kenneth558/plant_resistance_primary_perception_IN_DEVELOPMENT/the Biblical perspective.md

The principles relevant to the GWAAM-Sea Aid are found in several Bible verses, including the following:

Notice the name of the element within us that is being exercised when we practice this type of gardening:

 - If ye have faith, and doubt not, ye shall not only do this which is done to the fig tree, but also if ye shall 
   say unto this mountain, Be thou removed, and be thou cast into the sea; it shall be done. And all things,
   whatsoever ye shall ask in prayer, believing, ye shall receive. Matt 21:21-22

Notice the value God puts on that element:

 - But without faith it is impossible to please him    Heb. 11:6

Notice the pre-eminent importance of love (called "charity" in the KJV Bible; gr. "agape")

 - And now abideth faith, hope, charity, these three; but the greatest of these is charity. I Cor 13:13

Notice the acquisition order that will be acceptable for the beginner during their growth and maturation:

 - And beside this, giving all diligence, add to your faith virtue; and to virtue knowledge; And to knowledge
   temperance; and to temperance patience; and to patience godliness; And to godliness brotherly kindness; and to 
   brotherly kindness charity (love).   2 Peter 1:5

And finally, since Jesus made the connection between faith and prayer in that Matt. 21:22 verse above, notice the type of prayer and faith that will get things done:

 - The effectual fervent (the word "energetic" encapsulates both terms; gr. "energeo") prayer of a righteous man availeth much.

From all this, we see that developing the faith to affect plants is merely step 1 of a journey of which the destiny is love.  Stated another way, it will be very unbecoming, even ugly, for a person to exercise faith, yet not be intent on loving other people.

We also see from that verse that when we exert energy in support of our faith's actions that faith produces greater results.  Cleve Backster noticed the same thing in his experiments with plants.

Note that even though God values virtue, knowledge, and so on out to love more than faith, He'll be gracious to accept us to start with faith.

The elephant in the living room:  These teachings from heaven were kept hidden by God from the public until Jesus walked this earth and brought them to us.  Jesus says no one can come to the Father but through Jesus.  Although we've discovered that plants will respond to anyones' sentiments, thanks to the grace of God, God's real God-ordained starting point for our development along this path is Jesus:

 - "But as many as received him, to them gave he power to become the sons of God, even to them that believe on 
    his name"   John 1:12
    
What plants are recognizing in us is that mankind comes from a royal lineage.  God has placed us here intending that we choose that royalty once again, and in so doing, Jesus offers us a more abundant life:  "I am come that they might have life, and that they might have it more abundantly"   John 10:10  (the astute reader will notice additionally that Jesus has actually also come to give us life itself...there is something deep there for those who have an ear to hear...)

Jesus' statement in Matt. 21:21 is a prophecy that has yet to be fulfilled to the scale He stated it.  To the extent that we are now able to fulfill this good prophecy of His and we refuse to do so, we deprive Him of what He is worthy of.  I want to see that He is no longer deprived of the fulfillment of His words that He is worthy of.  With a little help from the real-time, instantaneous feedback that devices like the GWAAM-Sea Aid provide, people can learn the faith technique needed to bring fulfillment to that good prophecy of His.

## Wrap-up:</p>
Jesus cursed the fig tree, it withered away, and He said we would do the same [Matt 21:19-21](https://www.biblegateway.com/passage/?search=Matt+21%3A19-21&version=KJV):

#### 19 And when he saw a fig tree in the way, he came to it, and found nothing thereon, but leaves only, and said unto it, Let no fruit grow on thee henceforward for ever. And presently the fig tree withered away.
#### 20 And when the disciples saw it, they marvelled, saying, How soon is the fig tree withered away!
#### 21 Jesus answered and said unto them, Verily I say unto you, If ye have faith, and doubt not, ye shall not only do this which is done to the fig tree, but also if ye shall say unto this mountain, Be thou removed, and be thou cast into the sea; it shall be done.
#      
When we read this passage, we too often overlook the phrase "...ye shall not only do this which is done to the fig tree...".  But that oft-overlooked phrase contains just as profound a truth as the phrase following it about casting mountains!  Jesus did not condemn us if we should curse a plant, yet we must not forget [John 14:12](https://www.biblegateway.com/passage/?search=John+14%3A12&version=KJV):
#### Verily, verily, I say unto you, He that believeth on me, the works that I do shall he do also; and greater works than these shall he do; because I go unto my Father.
Ask yourself what a greater work might be than cursing a plant to kill it.  How about blessing a plant to cause its health to be better than normal?  [Mark 16:15](https://www.biblegateway.com/passage/?search=Mark+16%3A15&version=KJV):
#### And he said unto them, Go ye into all the world, and preach the gospel to every creature.
I draw your attention on the word "creature".  That includes plants!  And note that the definition of "gospel" is "good news"

In summary, Jesus accepted the fact that people would kill plants like fig trees with a curse but also said we will do greater than that.  It is with the hope that we will do far, *far* more of the latter than the former that I make the plans for this project freely available to everyone.  I am convinced that it is NOW time to demonstrate the truthfulness of the Bible in this context!  That is by monitoring the electrical resistance of plant tissue in vivo as it responds to sentiments of good news delivered to it from human beings that plants recognize as royalty in the creation.  To understate my point - it would be of great benefit for us to recognize that we are royalty, just as the plants recognize that humans are royalty in the creation.

[Galatians 4:1-7](https://www.biblegateway.com/passage/?search=Galatians+4%3A1-7&version=KJV):
#### 1 Now I say, That the heir, as long as he is a child, differeth nothing from a servant, though he be lord of all;
#### 2 But is under tutors and governors until the time appointed of the father.
#### 3 Even so we, when we were children, were in bondage under the elements of the world:
#### 4 But when the fulness of the time was come, God sent forth his Son, made of a woman, made under the law,
#### 5 To redeem them that were under the law, that we might receive the adoption of sons.
#### 6 And because ye are sons, God hath sent forth the Spirit of his Son into your hearts, crying, Abba, Father.
#### 7 Wherefore thou art no more a servant, but a son; and if a son, then an heir of God through Christ.

Notice in reading all this that the entirety of this project is Biblically based.  In fact, more specifically it is based in the words and lives of Jesus and His disciples.  God reserved these things to give to the believing Gentiles so they could make the nation of Israel jealous and know that they'll have to come back to God through Jesus.  Far be it from me to make it easy for anyone to short-circuit their way in without knowing that it was Jesus who started this whole agronomy-to-mountain-casting idea.  A mocker might posit that telempathic gardening probably came along well prior to Jesus' time, so Jesus didn't start it at all.  The fact is, Jesus actually was involved in started EVERYTHING well before He became a man, so He still knew first.
