kenneth558/plant_resistance_primary_perception_IN_DEVELOPMENT/embeddeds/adc primary perception ADS board ground pin cropped.png

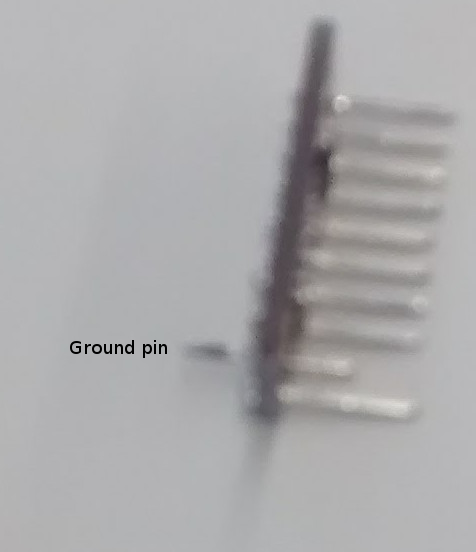
embeddeds/adc primary perception ADS board ground pin cropped.png
