kenneth558/plant_resistance_primary_perception_IN_DEVELOPMENT/embeddeds/onestepsizewobble.png

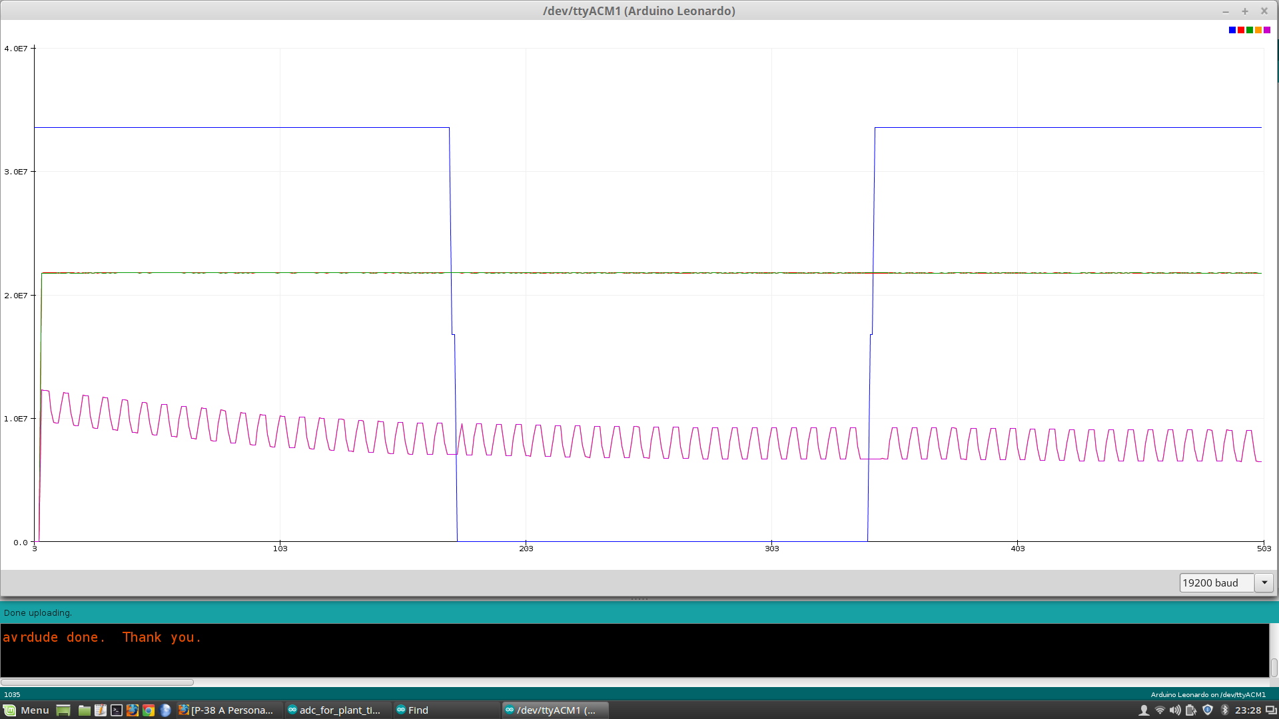
embeddeds/onestepsizewobble.png
