kenneth558/plant_resistance_primary_perception_IN_DEVELOPMENT/embeddeds/resposition_in_sync.png

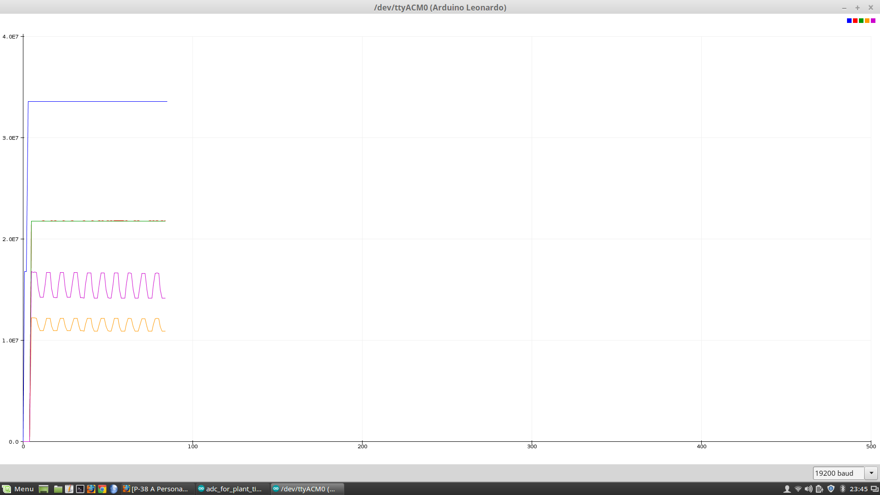
embeddeds/resposition_in_sync.png
