kenneth558/plant_resistance_primary_perception_IN_DEVELOPMENT/Where to find everything for making your own GWAAMC device/Quantum expansion.png

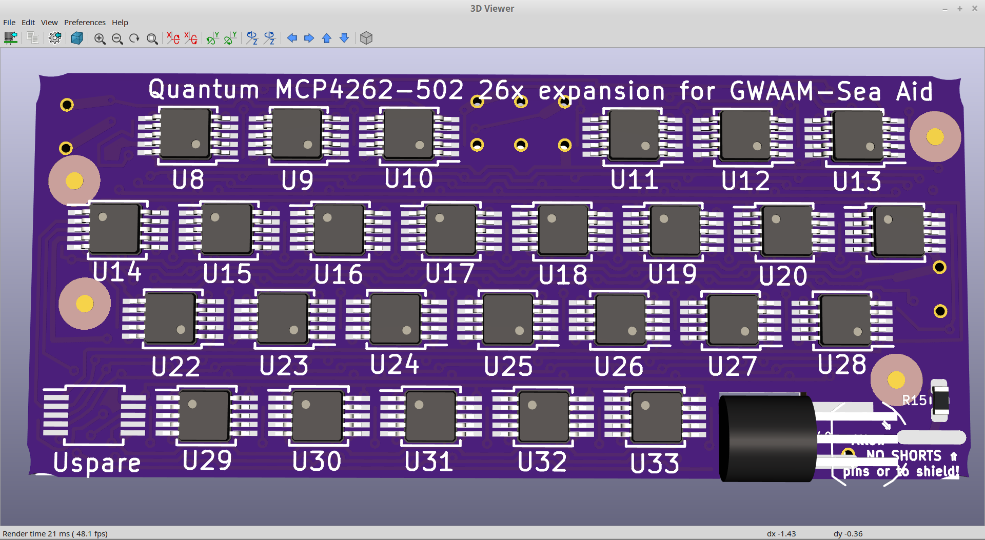
Where to find everything for making your own GWAAMC device/Quantum expansion.png
