kenneth558/plant_resistance_primary_perception_IN_DEVELOPMENT/Where to find everything for making your own GWAAMC device/uno shield v1.0 project SMD front oblique.png

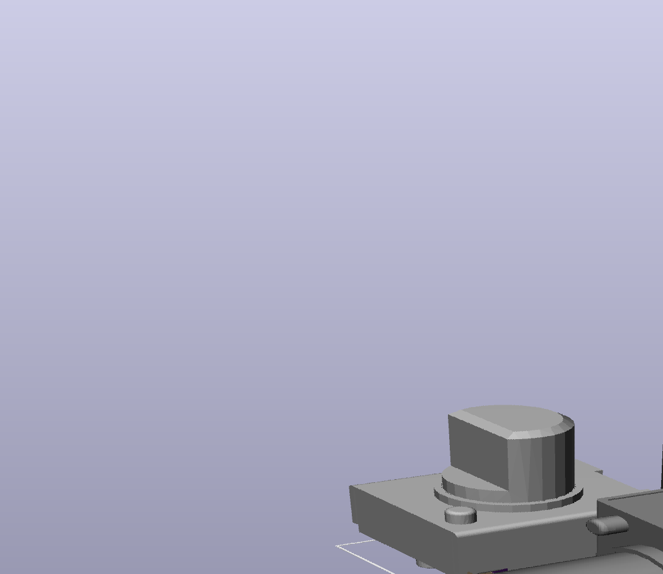
Where to find everything for making your own GWAAMC device/uno shield v1.0 project SMD front oblique.png
