kenneth558/plant_resistance_primary_perception_IN_DEVELOPMENT/sketch code/diags.ino

//        BEFORE COMPILING THIS SKETCH you must set or confirm the following preprocessor macros appropriately for your configuration and preferences !!!
#define LM334_BRIDGES 1                                        //Number of digipot Wheatstones you have topped with LM334s each leg, (schematically wired before bare DPot bridges) but this sketch revision level not tested beyond 1.  Remove if using Wheatstone bridge with only standard or DPot resistors.  make this the number of bridges with upper resistive elements being LM334s controllable with the MCP4162-104 pots
#define DPOTS_PER_LM334_LEG 2                                  //Not yet tested for any setting except 3, so verify it before trusting fully.  Due to their significant temperature coefficient, LM334s need to be used in pairs so their tempco offsets each other's; i.e., LM334 legs are invalid unless bridged with both legs topped by a LM334
#define INBOARDS_PLOTTED 2                              //The number of consecutive analog pins to plot, beginning with PIN_A0
//#define OUTBOARDS_PLOTTED 1                             //The number of consecutive "highest-sensitivity ADC" pins to plot, beginning with A0 and, if double-ended, A1.  OUTBOARD ADC ONLY - DOES _NOT_ INCLUDE INBOARD ANALOG INPUT PINS
//#define MAGNIFICATION_FACTOR 5                                 //Activates the plotting of magnified traces in all ADC linespaces; upper limit somewhere less than 4,294,967,295. Note: you can disable displaying magnified traces altogether by not defined this macro at all. Proper use of SUPERIMPOSE_FIRST_INBOARDS_IN_PAIRS will also disable magnified traces of the first two analog inputs
#define HIGHEST_SENSI_OUTBOARD_ADC_TYPE HX711                  //Proposing that "ADS1231" covers ADS1231; could make this "ADS1232" ( ADS1232), "ADS1242" ( ADS1242), "AD779x" ( AD779x), "AD7780" ( AD7780), "HX711" (HX711), "ADS1X15" ( ADS1015 or ADS1115), "MAX112x0" (MAX112X0...) or "LTC2400" (LTC2400) but code not included in v.FREE; ONLY ONE TYPE ALLOWED
#define HIGHEST_BIT_RES_FROM_HIGHEST_SENSI_OUTBOARD_ADC 24     //All ADC values will get scaled to the single-ended aspect of this,  15 is ADS1115 single-ended, 16 for double-ended when two LM334s are used.  change to 11 for ADS1015 single-ended or 12 with two LM334s, (future: change to 24 for HX711--NO b/c there is the ADS1231 at 24 bits)
#define SAMPLE_TIMES 2                                         //To better average out artifacts we over-sample and average.  This value can be tweaked by you to ensure neutralization of power line noise or harmonics of power supplies, etc.....
#define MINIMIZE_COMMUNICATIONS_CLUTTER_FOR_HIGHER_MAX_SPEED_ONLY_COMPATIBLE_FOR_OFFICIAL_ARDUINO_IDE false//Doesn't catch much - future plan is to have different levels including DEBUG in this
#define MOST_PROBLEMATIC_INTERFERENCE_FREQ 60                                                               //This is here just in case you think that you might have some interference on a known frequency.
#define DELAY_TIME_BETWEEN_SAMPLES_MS ( 1000 / MOST_PROBLEMATIC_INTERFERENCE_FREQ / SAMPLE_TIMES )          //COARSE ADJUST
#define DELAY_TIME_BETWEEN_SAMPLES_US ( ( ( 1000000 / MOST_PROBLEMATIC_INTERFERENCE_FREQ ) - ( DELAY_TIME_BETWEEN_SAMPLES_MS * SAMPLE_TIMES * 1000 ) ) / SAMPLE_TIMES ) //FINE ADJUST.  THIS GETS ADDED TO COARSE ADJUST, PRECISION = TRUNCATED PRAGMATICALLY TO uSec TO ACKNOWLEDGE SOME OVERHEAD FOR LOOPING SUPPORT CODE   // End of this part of code update
#define FIRST_ANALOG_PIN_DIGITAL_NUMBER_FOR_BOARDS_NOT_HAVING_ANALOG_PINS_DEFINED_BY_PIN_A0_TYPE_DEFINES 14 //Gets changed to 18 for Leonardo. Why this? Some boards don't have good definitions and constants for the analog pins :-(
#define PERCENT_OF_LINESPACE_MAGNIFIED_VIEW_SKIPS_WHEN_REPOSITIONED_WHEN_LINESPACE_LIMITS_GET_EXCEEDED 85   //BETWEEN 0 AND 100 indicating how much of the display region in percent to skip when magnified view trace has to get repositioned because trace would be outside region bounds; NO BOUNDS CHECKING IS PROVIDED!!!
#define ANALOG_INPUT_BITS_OF_BOARD 10                                        //Most Arduino boards are 10-bit resolution, but some can be 12 bits.  For known 12 bit boards (SAM, SAMD and TTGO XI architectures), this gets re-defined below, so generally this can be left as 10 even for those boards
#define SECONDS_THAT_A_LGT8FX8E_HARDWARE_SERIAL_NEEDS_TO_COME_UP_WORKING 9   //8 works only usually
#define HIGHEST_SENSI_PGA_GAIN_FACTOR 128                                     //PGA=Programmable Gain Amplifier: many ADCs will correlate a gain of one with full-scale being rail-to-rail, while a gain of anything higher correlates to full-scale being in the mV range (most sensitive and most noise-susceptible).  Set of allowable values: 64 and 128 will cause INA+/- to be read.  32 will cause INB+/- to be read. Defining POT_WIPER_TO_THIS_ANALOG_INPUT_PIN_TO_ADJUST_PGA_GAIN_FACTOR will override this macro
#define MIN_WAIT_TIME_BETWEEN_PLOT_POINTS_MS 1                               //Sets a maximum speed limit, but actual speed may be further limited by other factors
#define SUPERIMPOSE_FIRST_INBOARDS_IN_PAIRS 1                                //If defined allows the rail-to-rail inboard Analog Inputs to be used to adjust digipots, but mainly causes first inboard Analog Inputs to be paired (superimposed in pairs sharing plot-line spaces) so even manual pots can be adjusted easily.
//#define PLOT_ONLY_THE_SIGNAL_LEG_OF_SUPERIMPOSED_DPOT_LEG_BRIDGE_INBOARDS  //By defining this macro comparison between signal and reference is no longer possible but it could be less confusing this way since user doesn't need to manually adjust anything with DPots and especially with AUTO_BRIDGE_BALANCING. ADVISE without AUTO_BRIDGE_BALANCING in effect, this macro probably should not be defined either. But regardless for greatest flexibility, that macro won't affect this.
#define AUTO_BRIDGE_BALANCING                                                //is not perfectly robust yet in extremes and circuit faults, but will allow starting at a balanced level //increases setup time and during which the plot timing line stays high, then spikes low and high to indicate balancing complete //Turns on auto-balancing in setup(), significant time elapse for this to complete!
#define CONTINUE_PLOTTING_DURING_AUTO_BRIDGE_BALANCE true                    //Without predictive balancing, this takes too much time if true
//#define DEBUG                                                              //Don't forget that DEBUG is not formatted for Serial plotter, but might work anyway if you'd never print numbers only any DEBUG print line
#define COMPILE_FOR_DIAGS_ONLY
//#define DIAGS_STEP1                                                          //Optionally define on very first run of diags.
//#define DIAGS_STEP2                                                          //Don't define on very first run of diags
//#define DIAGS_STEP3                                                          //Don't define on very first run of diags
#define DIAGS_STEP4                                                          //Don't define on very first run of diags
#define SHOW_LINEARITY_USING_THIS_BRIDGE_INDEX 0                                    //Can be a single bridge index or the word "ALL"
#define INJECT_DIAGNOSTIC_SQUARE_WAVE_ON_SIGNAL_PIN_OF_SPECIFIED_OUTBOARD_ADC 0       //For testing - wobbles digipot settings on bridge index to impose a signal into Wheatstone bridge outputs. This imposes a signal on the signal leg
#define INJECT_DIAGNOSTIC_SQUARE_WAVE_ON_REFERENCE_PIN_OF_SPECIFIED_OUTBOARD_ADC 0    //For testing - wobbles digipot settings on bridge index to impose a signal into Wheatstone bridge outputs. This imposes a signal on the reference leg
#define DIAGNOSTIC_SQUARE_WAVE_TIME_PERIOD  10
//#define LEAVE_POT_VALUES_ALONE_DURING_SETUP                                         //First run should leave this undefined to load digi pots with some values
#define BIAS_IN_ANALOG_INPUT_BITS_TO_APPLY_TO_SIGNAL_LEG_TO_CENTER_THE_TRACE_BRIDGE0 0  //This offset will be applied to all signal lines of outboard ADCs, not just the first one, until further development.  Write some code yourself to expand.  Inboard Analog Inputs of 10 bits will make much change with little values, 12 bit inboard allows more flexibility here
#ifdef BIAS_IN_ANALOG_INPUT_BITS_TO_APPLY_TO_SIGNAL_LEG_TO_CENTER_THE_TRACE_BRIDGE0
#define ADDITIONAL_BIAS_IN_LSB_DPOT_SETTING_POSITION_TO_APPLY_TO_SIGNAL_TRACE_BRIDGE0 2 //To maintain consistent effect with the above, associated macro, this gets applied inverted. This is in lieu of setting by reading the ADCs and zeroing them.
#endif
#ifdef __LGT8FX8E__
#define BAUD_TO_SERIAL 19200                                                          //This speed is what works best with WeMos XI/TTGO XI board.  Experiment as desired.
#else
#define BAUD_TO_SERIAL 115200                                                         //YOU MAY SET THIS TO THE MAXIMUM VALUE THAT YOUR CONFIGURATION WILL FUNCTION WITH (UNLESS YOU'RE USING THE WeMos XI/TTGO XI, OF COURSE)
#endif
#define DPOT_RATIO ( signed )248 /* DPOT_RATIO: System-wide MSB/LSB.  Ex.: If the LSB digipot is 200 ohms/step and the MSB digipot is 2000 ohms/step, this value will be 10. (2000/200)
                      It is only used relative to the LSB digipot, so there can only be that one digipot per leg allowed to have a smaller resistance
                      per step than other digipots on the leg. All bridge legs in the system must be built with the same ratio scheme, and must always include one and
                      only one LSB digipot, with all non-LSB digipots matching each others' resistance/step values.  This macro limits LSB settings adjustments
                      when another digipot in the leg is set to less than MAX_DPOT_SETTG, but not otherwise, allowing LSB to reach MAX_DPOT_SETTG when non-LSBs are all at MAX_DPOT_SETTG.
                      As far as MAX_DPOT_SETTG, all digipots in the system are bound by the same MAX_DPOT_SETTG value. */
#define MINIMIZE_COMPILED_SKETCH_SIZE_LEVEL 9                                //Number 0 produces smallest sketch giving least data output functionality
#define LOOP_COUNTER_LIMIT_THAT_TRACE_IS_ALLOWED_TO_BE_OFF_CENTER 2          //sets how soon run-time auto-balancing kicks in when trace goes off scale
//#define POT_WIPER_TO_THIS_ANALOG_INPUT_PIN_TO_ADJUST_PGA_GAIN_FACTOR 3     //Overrides HIGHEST_SENSI_PGA_GAIN_FACTOR. NOT the digital number for pins! Is more like the leg index //Can use a spare analog input for gain adjustment by connecting wiper of a pot (100K or greater, please) that voltage-divides 0-5 vdc.  //Arduino pin only unless a dedicated ADS1115 is used

//FUTURE
//FUTURE #define BARE_DPOT_LEG_BRIDGES                       //(after LM334 bridges in terms of pin number order) Subject to change NOT CODED FOR YET.  Note that higher values of DPot leg resistances are expected to be required.  This could mean more DPots per leg increasing the likelihood 74LV138 decoding will be necessary.
//FUTURE #define BARE_DPOT_LEGS_UNBRIDGED                    //(after active bridges in terms of pin number order, passive bridges using manual pots might include these legs)Subject to change NOT CODED FOR YET.  Note that higher values of DPot leg resistances are expected to be required.  This could mean more DPots per leg.
//FUTURE #define DPOTS_PER_BRIDGED_BARE_LEG 3                //Might work now but not yet tested for any setting, so verify it before trusting fully
//FUTURE #define DPOTS_PER_UNBRIDGED_BARE_LEG 3              //Might work now but not yet tested for any setting, so verify it before trusting fully
//FUTURE #define SD_CHIP_SELECT_PIN 4                    //The free version does not contain the code to utilize SD card storage.  SD card storage only available in the priced ($20) sketch version.
//FUTURE #define WIFI true                                   //The free version does not contain the code to utilize wifi.  Wifi only available in the priced ($20) sketch version.  Buy online at http://GWAAMC.com
//FUTURE #define POT_WIPER_TO_THIS_ANALOG_INPUT_PIN_TO_ADJUST_MAGNIFICATION_FACTOR 4    //NOT the digital number for pins! Is more like the leg index //Can use a spare analog input as magnification attenuator by connecting wiper of a pot (100K or greater, please) that voltage-divides 0-5 vdc.  //Arduino pin only unless a dedicated ADS1115 is used
//FUTURE #define USING_DUAL_74LV138_DECODERS_FOR_DPOT_CS_LINES
//FUTURE #define TEST_STEP_UP_DOWN COMMONMODE                                // Available: SINGLESIDE COMMONMODE
//FUTURE #define BARE_DPOT_LEG_BRIDGES, BARE_DPOT_LEGS_UNBRIDGED             // Subject to change, but this makes effects of DPot settings be reversed from when LM334s are used.  Note that higher values of DPot leg resistances are expected to be required.  This could mean more DPots per leg.
//FUTURE #define BARE_DPOT_LEG_BRIDGES 1                                     // (after LM334 bridges in terms of pin number order) Subject to change NOT CODED FOR YET, but this makes effects of DPot settings be reversed from when LM334s are used.  Note that higher settingValues of DPot leg resistances are expected to be required.  This could mean more DPots per leg increasing the likelihood 74LV138 decoding will be necessary.
//FUTURE #define BARE_DPOT_LEGS_UNBRIDGED 1                                  //(If inputting to outboard ADCs these would be after active bridges in terms of pin number order, passive bridges using manual pots might include these legs)Subject to change NOT CODED FOR YET, but this makes effects of DPot settings be reversed from when LM334s are used.  Note that higher settingValues of DPot leg resistances are expected to be required.  This could mean more DPots per leg.
//FUTURE #define VERBOSITY_LEVEL                                             //To be used instead of and combines DEBUG and MINIMIZE_COMMUNICATIONS_CLUTTER_FOR_HIGHER_MAX_SPEED_ONLY_COMPATIBLE_FOR_OFFICIAL_ARDUINO_IDE
#ifdef USING_DUAL_74LV138_DECODERS_FOR_DPOT_CS_LINES                         //Arduino pins can be better utilized with higher numbers of DPots by adding 74LV138s expand the number of DPot CS pins that can be driven with a given number of Arduino pins
//!!! NOTE !!! 531 lines below this are also macros entitled similar to [NON_]LSB_DPOT_BXSIG(or REF)_PIN.  Those macros must also be set to correspond to the pins driving the CS lines of digipots
    #warning These pin numbers get specified normally, but be sure you specify the _digital_pot_CS_pins_ with the MSB set to decode them; i.e., make those pin numbers>= 128, but not these
    #define FIRST_STAGE_3_TO_8_DECODER_A0_PIN1 9                             //
    #define FIRST_STAGE_3_TO_8_DECODER_A1_PIN2 10                             //Second address pin of first stage not necessary if total DPots in the systems <= 2
    #define FIRST_STAGE_3_TO_8_DECODER_A2_PIN3 11                             //Third address pin of first stage not necessary if total DPots in the system <= 4
    //#define FIRST_STAGE_3_TO_8_DECODER_A3_PIN4 12                           //Always the same as FIRST_STAGE_3_TO_8_DECODER_ENABLE_PIN4 since both reference pin 4
    #ifndef FIRST_STAGE_3_TO_8_DECODER_A3_PIN4
        #define FIRST_STAGE_3_TO_8_DECODER_ENABLE_PIN4 13                     //Pin 4 either paralleled with final stage's pin 4 (only for up to 8 DPots) or used as a virtual A3. Pin 5 always connects to pin 4 of final stage 74LV138.
    #endif
    //#define FINAL_STAGE_3_TO_8_DECODER_A0_PIN1 9                           //Second stage not necessary if total DPots in the system <= 8
    //#define FINAL_STAGE_3_TO_8_DECODER_A1_PIN2 10                           //Second address pin of second stage not necessary if total DPots in the systems <= 16
    //#define FINAL_STAGE_3_TO_8_DECODER_A2_PIN3 11                           //Third address pin of second stage not necessary if total DPots in the systems <= 32
    //#define FINAL_STAGE_3_TO_8_DECODER_ENABLE_PIN4 12                       //This connects into both 74LV138 chips on their pins 4 with pins 6 held high. First stage gets its pin 5 signal from second stage pin 15 and second stage pin 5 gets held low. Maximum total DPots = 64
#endif                                                                       //There are two ways to use 74LV138s: if more than 16 DPots, then, in part, the final stage 74LV138 drives all previous stages 74LV138 with its output lines driving pin 4 of previous stages. Up to 16 DPots can be used by two 74LV138s in parallel with, in part, the first 74LV138's pin 4 acting as an A3 and its pin 5 connected to pin 4 of the final 74LV138

//No need to change macros below:
#define CONVERT_TWOS_COMP_TO_SINGLE_ENDED( value_read_from_the_differential_ADC, mask, xorvalue ) ((value_read_from_the_differential_ADC & mask)^xorvalue)
//A FEW OF THE OTHER MACROS (DEFINES OR RE-DEFINES) ELSEWHERE: VERSION, NON_LSB_DPOT_2_B0SIG_STARTVALUE - LSB_DPOT_B0REF_STARTVALUE, HALFHIGHEST_BIT_RES_FROM_HIGHEST_SENSI_OUTBOARD_ADC, DIFFERENTIAL, PIN_FOR_DATA_TOFROM_HIGHEST_SENSI_ADC, PIN_FOR_CLK_TO_HIGHEST_SENSI_ADC, PLOTTER_MAX_SCALE, HUNDREDTHPLOTTER_MAX_SCALE, SAMPLE_TIMES, SCALE_FACTOR_TO_PROMOTE_LOW_RES_ADC_TO_SAME_SCALE, COMMON_MODE_LEVEL_FOR_MAX_GAIN_AS_READ_RAW_BY_INBOARD_ANALOG, HEIGHT_OF_A_PLOT_LINESPACE
#define COPYRIGHT_YEAR "<2018>, <2019>"
/*******************(C) GNU General Public License COPYRIGHT 2019 KENNETH L ANDERSON *********************
       ARDUINO ELECTRICAL RESISTANCE/CONDUCTANCE MONITORING SKETCH
  File Name          : adc_for_plant_tissue.ino
  Author             : KENNETH L ANDERSON
  Version            : v.Free
  Date               : 07-OCT-2019
  Description        : To replicate Cleve Backster's findings that he attributed to a phenomenon he called "Primary Perception".  Basically, this sketch turns an Arduino MCU and optional ADS1115 or HX711 (recommended) into a nicely functional GSR (Galvanic Skin Response) device or poor man's polygraph) in order to learn/demonstrate telempathic gardening.
  Boards tested on   : Uno using ADS1115 (early version), HX711, and inboard analog inputs.
                     : TTGO XI using ADS1115 in an early version
                     : Many other configurations should work fine.
                     : The ATtiny x4, ATtiny x5, ATtiny x61, ATtiny x8  not suitable at all due to not having hardware serial
  Known limitations  : Free version does not use predictive auto bridge balance resulting in painfully slow auto balance when plant conductance goes out of range
                     : Free version does not utilize microcontroller interrupts, so has a lower speed limitation than the professional version
                     : No ability to accept user input from keyboard during run time due to Arduino plotter limitation
                     : Re-compile always needed to effect any changes to configuration
                     : Analog input pins being used are hard-coded to be used in pin number order and their purposes are hard-coded as well
                     : Only a single add-on ADS ADC device and only 1 or 2 differential channels on it is tested
                     : Conventional add-on high-sensitivity ADCs limit their useable common mode differential input range to merely a few millivolts with active or passive clamping
                     : Non-bridged DPot legs are only for outboard ADCs though presumeably single-ended, they are not accommodated for inboard Analog Inputs
                     : Some of these limitations will be addressed in future not-for-free professional versions
      Due to the many preprocessor condition checks throughout this sketch source, the IDE is unable to track bracketed constructs accurately in many places.  What does this
      mean?  If you are used to relying on the IDE's highlighting of a paired bracket to help you know a bracketed construct's boundaries, you'll have to give that convenience up in places in this sketch source code.
********************************************************************************
  THE PRESENT PRODUCT WHICH IS ONLY FOR USE BY SOFTWARE- AND HARDWARE-COMPETENT 
  USERS IS INTENDED TO OFFER VARIOUS CAPABILITIES.  Because absolutely no 
  consideration is expected in return, no contract binding on me, whether offering
  suitability, reliability, functionality, safety, or other, exists.  IF YOU 
  MODIFY THIS SKETCH, I VERY SIMPLY REQUIRE that you not remove, hide, nor 
  denigrate the comments nor data output that refers to Jesus or God or their 
  words in any way.  BY USING THIS PRODUCT YOU EXPRESSLY AND TOTALLY ACCEPT FULL
  LIABILITY for any direct, indirect or consequential damages with respect to any 
  claims arising from software and/or hardware derivations of product. I make 
  absolutely no claim of my own competence, licensure, certification, experience,
  or professional standing other than being an Electronics Technician by formal 
  degree and United States FCC Radiotelephone Operators license, and a software
  developer by limited practical experience, and being formally degreed with 
  Bachelor of General Studies majoring in General Sciences
********************************************************************************
   Changelog:  17 Aug   2019 :  Start adding diags for building the board
               17 Apr   2019 :  Further fixes to allow MCP42xx dual digi-pots - lines 1048 and 1050 pin check changed to 0x40 from 0x400
               15 Apr   2019 :  First use of MCP4262s (instead of MCP4162s) and electrode connect indicator LEDs
               30 Mar   2019 :  Further fixes to allow MCP42xx dual digi-pots
               15 Feb   2019 :  Incorporates run-time gain adjustment with potentiometer wiper connected to Analog Input pin POT_WIPER_TO_THIS_ANALOG_INPUT_PIN_TO_ADJUST_PGA_GAIN_FACTOR when HX711 is used.  ADC inputs channel A will need to be wired parallel with channel B inputs.  Manufacturer will use 3-position switch with two 470K resistors in series between Vcc and GND and the middle switch position connects to middle of the resistor network, other two switch positions connect to Vcc and GND.
               24 Jan   2019 :  In process of modifying linearity diags to accommodate far higher resistances than I originally expected.  Hopefully the circuit itself won't need any modifications.
               21 Jan   2019 :  Reversed the order of traces plotted so that the outboard ADC is in the top group.
               18 Jan   2019 :  Predictive auto-balance working great by adding a fudge factor rather than fixing the formula the rational way
               15 Jan   2019 :  Auto-adjust working pretty fair, but haven't done thorough testing
               14 Jan   2019 :  Auto-adjust working crudely
               14 Jan   2019 :  Fixed the bugs relative to operation other than auto-balancing (auto-adjust).  Auto-adjust still not working beyond setup(), but at least this reversion level sets the bridge balances by the end of setup() when AUTO_BRIDGE_BALANCING is defined
               06 Jan   2019 :  After extensive changes to make this sketch flexible enough to incorporate the enhancements I had in mind I finally got this working in large part
               12 Dec   2018 :  Working on Predictive DPot setting, sketch is published for the purpose of establishing code flow to best support project advancement. 
               28 Nov   2018 :  Begin development on SD card storage + wifi connectivity so training aid can be powered through the power connector and store the data onboard and transmit it online
               17 Nov   2018 :  Functionalities restored that were present before scalability rewrite.
               16 Nov   2018 :  Scalability rewrite.  DO NOT USE PREDATED VERSIONS TO ADVANCE DEVELOPMENT!!!!!!!  Many changes have been made as of this date to accommodate future scalability
               18 Oct   2018 :  Now allows dual digi pot devices: MCP42xxx by manipulating the DPotPin of the first DPot of pkg OR'ing it with 0x40 as the pin of the second DPot in the pkg
               20 Sep   2018 :  Alpha chars added into output for future expansion beyond Arduino
               20 Sep   2018 :  Auto adjust works, but only non-predictively so it is slow.  Added macro CONTINUE_PLOTTING_DURING_AUTO_BRIDGE_BALANCE thinking someone may not want display to pause during auto balance, but that is even painfully slower still.
               11 Sep   2018 :  Back with new style of arrays useage to make bug-free coding more possible.
               23 Aug   2018 :  Fixed magnified traces in all respects; added functionality to display digipot calibration effects during calibration in setup(); started adding code to handle multiple digipot stacks that utilize dual 74VHC138/74LV138s.  Still no AUTO_BRIDGE_BALANCING
               23 Aug   2018 :  added USING_DUAL_74LV138_DECODERS_FOR_DPOT_CS_LINES with possibly enough code (just needs testing). Allowed for any ratio of LSB pot step to MSB step with DPOT_RATIO
               23 Aug   2018 :  Magnification factor adjustable downward via a potentiometer if defined POT_WIPER_TO_THIS_ANALOG_INPUT_PIN_TO_ADJUST_MAGNIFICATION_FACTOR with the digital number of an inboard analog input pin.
               01 Aug   2018 :  Working on vertical positioning of the magnified traces
               31 July  2018 :  I've noticed one sketch bug in the printing of the magnified traces in that they don't stay within bounds any more. Older sketch versions never had that problem. I'm not sure where it began, but it seems to be a memory management problem from my inital troubleshooting rather than any type of algorithm weakness. I'll work on that when I'm able...
               30 July  2018 :  Now able continuously to run-time auto-balance at least with a single HX711 LATER REVISIONS BROKE AUTO_BRIDGE_BALANCING
               29 July  2018 :  With INBOARDINPARALLELWITHHIGHESTSENSI && AUTO_BRIDGE_BALANCING defined, plotspace now excludes the two inboard Analog Input traces, making maximum linespace available for the other more interesting traces
               28 July  2018 :  If using digipots with LM334s, sketch can now auto-balance during setup and target the most sensitive common-mode voltage of a selected outboard ADC...LATER REVISIONS BROKE AUTO_BRIDGE_BALANCING
               27 July  2018 :  Discovered HX711's common-mode level sweet spot for max sensitivity, made COMMON_MODE_LEVEL_FOR_MAX_GAIN_AS_READ_RAW_BY_INBOARD_ANALOG with default of half-scale
               26 July  2018 :  Corrected conversion from twos complement differential readings to proper single ended plotting
               20 July  2018 :  Improved plotting with INBOARDINPARALLELWITHHIGHESTSENSI and improved 24-bit plot values
               16 July  2018 :  Removed disparaging comments toward TTGO XI/Wemo XI because we will make the plunge to employ the AD8244 buffer as standard, resulting in those boards being eligible as any other board
               15 July  2018 :  Allow unique digipot initializing settingValue for each pot.  Discovered HX711 input Z is way too low for use without buffers.  Regrouping....
               14 July  2018 :  Improved horizontal timing trace notching - made it shorter and consistent between levels
               13 July  2018 :  Modified plotter timing trace to notch horizontally at range min and max for signal traces when it crosses up and down.  Incorporated digi pot adjustings in debug mode. Enabled bypass of digi pot set in setup()
               18 June  2018 :  Bug fixes relative to displaying multiple traces while one or more are from inboard analog pins
               17 June  2018 :  Corrected pointer reinitialize of analogPinArray that disabled internal Analog Input pins.  Added "while( !Serial );" for Leonardo's native USB; starting to add framework for programmable potentiometers, changed defines to allow for a separate full-scale, lower res ADC and a high res ADC for normal viewing, etc,
               08 June  2018 :  Bugfix for inboard analog inputs above the first one - they didn't print before this fix
               05 June  2018 :  HX711 accommodated, you'll just have to balance the bridge manually
               32 May   2018 :  Added skeleton preprocessor defines for user to compatibly code their own support for a few 24-bit ADCs
               29 May   2018 :  Differential use of ADS1x15 to allow LM334 temperature comp to negative inputs so LM334 can be used on positive inputs
               18 May   2018 :  Anti-aliasing code
               04 May   2018 :  Some 12 bit tweaking so that TTGO/WeMos XI, SAM and SAMD architectures compile with inboard analog inputs to computed at 12 bit even though ANALOG_INPUT_BITS_OF_BOARD is set at default.
               30 April 2018 :  Final inboard 10 bit operation and ADS1X15 operation has been achieved.
               NEXT          :  Predictive DPot setting by tracking +/- Inboard and Outboard ADC bits per +LSB bit
               NEXT          :  Allow using dual digital potentiometers (MCP42XXX) for more lower parts count than when using single pot MCP41XXX
               NEXT          :  EEPROM storage of things like ADC sweet spot, initial digipot settings, etc.  Hardware configs like DPot types & ADC types & other upgradeable hardware version possiblities needs to be able to be set in the hat board rather than EEPROM
               NEXT          :  Accommodate ADS1232 &/or ADS1231
               NEXT          :  Detect hat config and version with 256 versions detection and warning to acquire more recent sketch version when versions > known are found
  TODO:  Arrange for run-time keyboard input to eliminate need to re-compile when changes are made or plotting adjustments are desired.  Will require non-Arduino IDE plotter
         Accommodate more 24-bit adcs like ADS1231
         Accommodate plant growth rate data somehow...visual/optical/height?
         Use interrupts to acquire in the background from ADCs so their always current readings will need no delay to read them as is the case when on demand direct from the device
   These planned enhancements will be reserved for NOT-FOR-FREE sketch versions in the future
  Planned longer-term upgrades are as follows:
  - Am currently coding for diagnostics useful when building the board.
  - Am currently coding for use of less than 3 and more than 3 DPots/leg
  - Am currently coding for using DPots alone, without LM334, in the bridges
  - Am currently coding for using unbridged DPots, single leg only
  - Am currently coding for faster conductance range changes when DUT conductance goes out of range
  - Not coding for other ADC types yet, but will eventually first code for multiple HX711

  Names are created according to the following conventions:
    PREPROCESSOR_MACROS (ALL_WORDS_IN_ALL_CAPS_AND_JOINED_WITH_DELINEATORS)
    functionNames
        and
    variableNames (eachWordCapitalizedExceptFirst, words joined without delineators)
    OBJECTNAMES (ALLWORDSINALLCAPS, words joined without delineators)
    struct_names (no_capital_letters, words joined with delineators)
    StructMemberNames
        and
    GotoLabels(EachWordCapitalized, words joined without delineators)
Leonardo note:
"The Leonardo has 12 analog inputs, labeled A0 through A11, all of which can also be used as digital i/o. Pins A0-A5 appear in the same locations as on the Uno; inputs A6-A11 are on digital i/o pins 4, 6, 8, 9, 10, and 12 respectively. "
    - taken from https://www.arduino.cc/en/Main/Arduino_BoardLeonardo
Elsewhere 
*********************************************************************************************************************/
#if ( defined ARDUINO_attiny )
    #error The board you are compiling for does not have the serial in its hardware that this sketch as written is dependent on.  Sorry...
#elif ( defined ARDUINO_ARCH_STM32F4 )
    #error The board you are compiling for has not been accommodated with this sketch as written is dependent on.  Sorry...
#endif
#define VERSION "v.Free"
#include <math.h>
#include <EEPROM.h> // Any board that errors compiling this line is unsuitable to be used for this purpose because it cannot store settings persistently
#ifdef WIFI  //The free version does not contain the code to utilize wifi.  Wifi only available in the priced ($20) sketch version.  
    #error The free version does not contain the code to utilize wifi.  Wifi only available in the priced ($20) sketch version.  Thank you for your understanding
    #include <Ethernet.h>
    #include <Phpoc.h> //This would necessitate a pricey shield
    #include <PhpocExpansion.h>
//Object gets instantiated during setup() for greatest flexibility
#endif
#ifdef SD_CHIP_SELECT_PIN  //The free version does not contain the code to utilize SD card storage.  SD card storage only available in the priced ($20) sketch version.
    #error  The free version does not contain the code to utilize SD card storage.  SD card storage only available in the priced ($20) sketch version.
    #ifndef SPIINCLUDED
        #include "SPI.h" //This is the hardware implementation of SPI with CS pin addressable devices (instead of devices with unidirectional data in and data out pins needing addressed via data).  The software implementation uses shiftIn() instead and is slower but frees up otherwise-CS pins and can be used adjunctive for cases where a chip has no CS pin.  Adafruit_ADS1015 uses the shiftIn() method, so those pins are user's choice.  Not data addressable as would be in I2C
        #define SPIINCLUDED
    #endif
    #include <SD.h>
    boolean bLogging;
    unsigned int logging_address = EEPROMlength - sizeof( boolean );
//Object gets instantiated during setup() for greatest flexibility
#endif

#undef BAUD_RATE
#define BAUD_RATE 57600 //Very much dependent upon the capability of the host computer to process talkback data, not just baud rate of its interface
#if not defined ( __LGT8FX8E__ ) && not defined ( ARDUINO_AVR_YUN ) && not defined ( ARDUINO_AVR_LEONARDO ) && not defined ( ARDUINO_AVR_LEONARDO_ETH ) && not defined ( ARDUINO_AVR_MICRO ) && not defined ( ARDUINO_AVR_ESPLORA ) && not defined ( ARDUINO_AVR_LILYPAD_USB ) && not defined ( ARDUINO_AVR_YUNMINI ) && not defined ( ARDUINO_AVR_INDUSTRIAL101 ) && not defined ( ARDUINO_AVR_LININO_ONE )
    #ifndef RESTORE_FACTORY_DEFAULTS
        #define RESTORE_FACTORY_DEFAULTS
    #endif
#else
    #if defined ( __LGT8FX8E__ )
        #define BAUD_RATE 19200 //During sketch development it was found that the XI tends to revert to baud 19200 after programming or need that rate prior to programming so we can't risk setting baud to anything but that until trusted in the future
        #define LED_BUILTIN 12
//Commonly available TTGO XI/WeMo XI EEPROM library has only .read() and .write() methods, no EEPROM.length().
        #define EEPROMlength 1024
        #define NUM_DIGITAL_PINS 14  //here if necessary or FYI.  TTGO XI has no D13 labeled but it's prob sck, https://www.avrfreaks.net/comment/2247501#comment-2247501 says why D14 and up don't work digital: "lgt8fx8x_init() disables digital with DIDR0 register.   Subsequent pinMode() should enable/disable digital as required.   i.e. needs a patch in wiring_digital.c"
    #endif
#endif
#ifndef EEPROMlength
    #define EEPROMlength EEPROM.length()
#endif


//global variables are declared static to prevent them from being seen by any later user-added compilation units that would try, presumeably inadvertently, through the use of the "extern" cast.  Feel free to change if not inadvertent access is helpful
//Next, force all macros to be coherent with each other
#ifndef OUTBOARDS_PLOTTED
    #define OUTBOARDS_PLOTTED 0
#elif ( 1 > OUTBOARDS_PLOTTED + 0 ) //Evaluates to 1>+0 if the macro was defined as a blank.  Only way I know of to check for blank macros when we need a number in them
    #undef OUTBOARDS_PLOTTED
    #define OUTBOARDS_PLOTTED 0
#endif
#if ( ( defined ARDUINO_ARCH_XI-ORIGINAL ) || ( defined ARDUINO_ARCH_XI ) || ( defined ARDUINO_ARCH_SAM ) || ( defined ARDUINO_ARCH_SAMD ) ) //These are the boards known to have 12 bit analog inputs
    #ifdef ANALOG_INPUT_BITS_OF_BOARD
        #undef ANALOG_INPUT_BITS_OF_BOARD
    #endif
    #define ANALOG_INPUT_BITS_OF_BOARD 12  //These boards have 12 bit
#endif

#define COMMON_MODE_LEVEL_FOR_MAX_GAIN_AS_READ_RAW_BY_INBOARD_ANALOG ( 1 << ( ANALOG_INPUT_BITS_OF_BOARD - 1 ) ) // Needed if HIGHEST_SENSI_OUTBOARD_ADC_TYPE has a sweet spot of max sensitivity, unlike true op-amp.  (HX711 == 306; normal op-amp, which has none == Vcc/2 == 512)
#ifndef INBOARDS_PLOTTED
    #define INBOARDS_PLOTTED 0 //This is used for some lightly thought out formulas in any case, so it must be defined until formulas are re-written to handle null values, but that might not be desirable as it results in more confusing formulas
#elif ( 1 > INBOARDS_PLOTTED + 0 )
    #undef INBOARDS_PLOTTED
    #define INBOARDS_PLOTTED 0
#endif
#ifdef MAGNIFICATION_FACTOR
    #if ( MAGNIFICATION_FACTOR == 0 ) //This value not allowed, assume it to mean 1
        #undef MAGNIFICATION_FACTOR
        #define MAGNIFICATION_FACTOR 1
    #endif
#endif
#ifdef ADDITIONAL_BIAS_IN_LSB_DPOT_SETTING_POSITION_TO_APPLY_TO_SIGNAL_TRACE_BRIDGE0
    #if ( ADDITIONAL_BIAS_IN_LSB_DPOT_SETTING_POSITION_TO_APPLY_TO_SIGNAL_TRACE_BRIDGE0 + 1 > 1 )
    #else
        #undef ADDITIONAL_BIAS_IN_LSB_DPOT_SETTING_POSITION_TO_APPLY_TO_SIGNAL_TRACE_BRIDGE0
    #endif
#endif
#ifdef ARDUINO_AVR_LEONARDO
    #undef FIRST_ANALOG_PIN_DIGITAL_NUMBER_FOR_BOARDS_NOT_HAVING_ANALOG_PINS_DEFINED_BY_PIN_A0_TYPE_DEFINES
    #define FIRST_ANALOG_PIN_DIGITAL_NUMBER_FOR_BOARDS_NOT_HAVING_ANALOG_PINS_DEFINED_BY_PIN_A0_TYPE_DEFINES 18 //Just saying...  Since the Leonardo has the A0 etc. #defines this won't come into play, but is here for reminder how things are
#endif
#define COMMON_MODE_LEVEL_FOR_MAX_GAIN_OF_UNPLOTTED_ADC_AS_READ_RAW_BY_INBOARD_ANALOG ( signed )307 //We do this for an example how we can configure for setting to a level without actually compiling for any outboard ADCs
#if ( OUTBOARDS_PLOTTED > 0 ) //Since so many of the ADC libraries already use OO classes, we'll set that as a pattern - instantiate prior to executing any code
    #define BITS_TO_LEFT_SHIFT_TO_KEEP_HIGH_RESOLUTION 6 //Used in predictive steping
    #define HALFHIGHEST_BIT_RES_FROM_HIGHEST_SENSI_OUTBOARD_ADC ( HIGHEST_BIT_RES_FROM_HIGHEST_SENSI_OUTBOARD_ADC / 2 )
    #if ( ( HALFHIGHEST_BIT_RES_FROM_HIGHEST_SENSI_OUTBOARD_ADC * 2 ) == HIGHEST_BIT_RES_FROM_HIGHEST_SENSI_OUTBOARD_ADC )
        #define DIFFERENTIAL
    #else
        #ifdef DIFFERENTIAL
            #undef DIFFERENTIAL
        #endif
    #endif
/*  The foloowing section needs further thought if to be used
    #if not ( ( ( defined MINIMIZE_COMPILED_SKETCH_SIZE_LEVEL ) && ( MINIMIZE_COMPILED_SKETCH_SIZE_LEVEL == 0 ) ) && ( ( not defined MINIMIZE_COMMUNICATIONS_CLUTTER_FOR_HIGHER_MAX_SPEED_ONLY_COMPATIBLE_FOR_OFFICIAL_ARDUINO_IDE ) || ( MINIMIZE_COMMUNICATIONS_CLUTTER_FOR_HIGHER_MAX_SPEED_ONLY_COMPATIBLE_FOR_OFFICIAL_ARDUINO_IDE == false ) ) )
        #ifdef MINIMIZE_COMMUNICATIONS_CLUTTER_FOR_HIGHER_MAX_SPEED_ONLY_COMPATIBLE_FOR_OFFICIAL_ARDUINO_IDE
            #undef MINIMIZE_COMMUNICATIONS_CLUTTER_FOR_HIGHER_MAX_SPEED_ONLY_COMPATIBLE_FOR_OFFICIAL_ARDUINO_IDE
        #endif
        #define MINIMIZE_COMMUNICATIONS_CLUTTER_FOR_HIGHER_MAX_SPEED_ONLY_COMPATIBLE_FOR_OFFICIAL_ARDUINO_IDE true
    #endif
*/
    #if ( HIGHEST_SENSI_OUTBOARD_ADC_TYPE == ADS1X15 ) && ( HIGHEST_BIT_RES_FROM_HIGHEST_SENSI_OUTBOARD_ADC < 17 ) && ( OUTBOARDS_PLOTTED > 0 )
        #include <Adafruit_ADS1015.h> //for systems using ADS1115/ADS1015  Data addressable I2C, shares bidirectional, open-collector data and clk only with other I2C slaves on same bus, must use the core-defined SDA/SCL pins except ESP8266 and ATtiny85 or see https://www.arduino.cc/en/reference/wire or see the Adafruit_ADS1X15-master README.md
    /*
       With Adafruit_ADS1015.h, SDA, SCL Wemos XI/TTGO XI use A4 for SDA, and A5 is SCL.
    */
        #if ( HIGHEST_BIT_RES_FROM_HIGHEST_SENSI_OUTBOARD_ADC == 15 ) || ( HIGHEST_BIT_RES_FROM_HIGHEST_SENSI_OUTBOARD_ADC == 16 )
            Adafruit_ADS1115 ads;  //For when ADS1115 is being used Data addressable I2C and shares bidirectional, open-collector data and clk only with other I2C slaves on same bus, must use the core-defined SDA/SCL pins except ESP8266 and ATtiny85 or see https://www.arduino.cc/en/reference/wire or see the Adafruit_ADS1X15-master README.md
        #else
            #if ( HIGHEST_BIT_RES_FROM_HIGHEST_SENSI_OUTBOARD_ADC == 11 ) || ( HIGHEST_BIT_RES_FROM_HIGHEST_SENSI_OUTBOARD_ADC == 12 )
                Adafruit_ADS1015 ads;  //For when ADS1015 is being used Data addressable I2C and bidirectional, open-collector data and clk only with other I2C slaves on same bus, must use the core-defined SDA/SCL pins except ESP8266 and ATtiny85 or see https://www.arduino.cc/en/reference/wire or see the Adafruit_ADS1X15-master README.md
            #else
                #error This add-on ADC resolution is not supported in this sketch version.
            #endif
        #endif
    #else
        #define PIN_FOR_DATA_TOFROM_HIGHEST_SENSI_ADC 2 //PROPRIETARY, NOT SPI Must always be dedicated in cases where it doesn't go hi-Z (as in HX711).  This won't work if an ADS1x15 or any other I2C device is also used on this pin
        #define PIN_FOR_CLK_TO_HIGHEST_SENSI_ADC 3 //PROPRIETARY, NOT SPI Must always be dedicated in cases where it doesn't go hi-Z (as in HX711).  This won't work if an ADS1x15 or any other I2C device is also used on this pin
    /*
       If ever would use an ADS1x15 along with this ADC, then see error msg below
            #ifdef ARDUINO_AVR_LEONARDO
                #if ( PIN_FOR_DATA_TOFROM_HIGHEST_SENSI_ADC == 2 ) || ( PIN_FOR_CLK_TO_HIGHEST_SENSI_ADC == 3 ) || ( PIN_FOR_CLK_TO_HIGHEST_SENSI_ADC == 2 ) || ( PIN_FOR_DATA_TOFROM_HIGHEST_SENSI_ADC == 3 )
                    #error "The pins being used for clock and data of the ADC conflict with the I2C pins used by ADS1x15.  See https://www.arduino.cc/en/reference/wire and the Adafruit_ADS1X15-master README.md.  Remove this warning once you are satisfied one way or another"
                #endif
            #endif
    */
        #if ( HIGHEST_SENSI_OUTBOARD_ADC_TYPE == HX711 ) && ( HIGHEST_BIT_RES_FROM_HIGHEST_SENSI_OUTBOARD_ADC == 24 )  //The HX711 does NOT communicate over open-collector I2C; pick your own pins for comming with it other than SS, CLK, MOSI, and MISO of SPI.  The digital interface to the HX711 is a proprietary SPI-like interface using CLK to select and Data is always lo-z (can't share either)
            #include <HX711.h>  //From https://github.com/bogde/HX711  This ADC has no CS pin so the library must use software SPI with dedicated CLK pin.  Not data selectable as would be in I2C, nor CS selectable - must be on dedicated CLK & Data lines
            HX711 hx711; // This library allows us to set the pins and gain here or later in a .begin().
            #undef COMMON_MODE_LEVEL_FOR_MAX_GAIN_AS_READ_RAW_BY_INBOARD_ANALOG
            #define COMMON_MODE_LEVEL_FOR_MAX_GAIN_AS_READ_RAW_BY_INBOARD_ANALOG 307                // If HIGHEST_SENSI_OUTBOARD_ADC_TYPE has a sweet spot of max sensitivity, unlike true op-amp.  (HX711 == 307, ranging from 1.49 to 1.507 vdc depending which scale is used to read it).  This will also be discovered and stored in EEPROM in a future revision
        #elif ( HIGHEST_SENSI_OUTBOARD_ADC_TYPE == ADS1232 ) && ( HIGHEST_BIT_RES_FROM_HIGHEST_SENSI_OUTBOARD_ADC == 24 )
        #elif ( HIGHEST_SENSI_OUTBOARD_ADC_TYPE == ADS1242 ) && ( HIGHEST_BIT_RES_FROM_HIGHEST_SENSI_OUTBOARD_ADC == 24 ) //Which 24-bit ADC is single-ended?  ADS1242 It is 23 bits hopefully
        #elif ( HIGHEST_SENSI_OUTBOARD_ADC_TYPE == AD7780 ) && ( HIGHEST_BIT_RES_FROM_HIGHEST_SENSI_OUTBOARD_ADC == 24 )
        #elif ( HIGHEST_SENSI_OUTBOARD_ADC_TYPE == AD779x ) && ( HIGHEST_BIT_RES_FROM_HIGHEST_SENSI_OUTBOARD_ADC == 24 )
        #elif ( HIGHEST_SENSI_OUTBOARD_ADC_TYPE == MAX112x0 ) && ( HIGHEST_BIT_RES_FROM_HIGHEST_SENSI_OUTBOARD_ADC == 24 )
        #elif ( HIGHEST_SENSI_OUTBOARD_ADC_TYPE == LTC2400 ) && ( HIGHEST_BIT_RES_FROM_HIGHEST_SENSI_OUTBOARD_ADC == 24 )
        #elif ( HIGHEST_SENSI_OUTBOARD_ADC_TYPE == ADS1231 ) && ( HIGHEST_BIT_RES_FROM_HIGHEST_SENSI_OUTBOARD_ADC == 24 )
        #else
            #error This add-on ADC resolution is not supported in this sketch version
        #endif
    #endif
#else
    #define BITS_TO_LEFT_SHIFT_TO_KEEP_HIGH_RESOLUTION 0
    #ifdef HIGHEST_BIT_RES_FROM_HIGHEST_SENSI_OUTBOARD_ADC
        #undef HIGHEST_BIT_RES_FROM_HIGHEST_SENSI_OUTBOARD_ADC
    #endif
    #define HIGHEST_BIT_RES_FROM_HIGHEST_SENSI_OUTBOARD_ADC ANALOG_INPUT_BITS_OF_BOARD
//    #ifdef HIGHEST_SENSI_OUTBOARD_ADC_TYPE
//        #undef HIGHEST_SENSI_OUTBOARD_ADC_TYPE //this would prevent setup from finding linearity unless outboard ADC was operating: undesireable limitation
//    #endif
    #ifdef HIGHEST_SENSI_PGA_GAIN_FACTOR
        #undef HIGHEST_SENSI_PGA_GAIN_FACTOR
    #endif
#endif
#define RED_LED_PIN 6 //ALL LED pins must be in a contiguous block that begins with both LED pins for ADC(0)
#define YELLOW_LED_PIN 5 //ALL LED pins must be in a contiguous block that begins with both LED pins for ADC(0)
#ifndef LOOP_COUNTER_LIMIT_THAT_TRACE_IS_ALLOWED_TO_BE_OFF_CENTER
    #define LOOP_COUNTER_LIMIT_THAT_TRACE_IS_ALLOWED_TO_BE_OFF_CENTER 65536 //really bad idea, will crash at some point
#endif
#ifndef BIAS_IN_ANALOG_INPUT_BITS_TO_APPLY_TO_SIGNAL_LEG_TO_CENTER_THE_TRACE_BRIDGE0
    #define BIAS_IN_ANALOG_INPUT_BITS_TO_APPLY_TO_SIGNAL_LEG_TO_CENTER_THE_TRACE_BRIDGE0 0
#endif
#if ( INBOARDS_PLOTTED > 0 )
    #ifndef NUM_ANALOG_INPUTS
        #error You are compiling for a board that requires you to manually define the define variable NUM_ANALOG_INPUTS somewhere above this line and re-compile...
    #endif
#else
    #if ( OUTBOARDS_PLOTTED == 0 )
        #error You will need to manually define at least one of the variables INBOARDS_PLOTTED or OUTBOARDS_PLOTTED where they appear in the lines above and re-compile...
If you only have the Arduino without an ADS1X15, then define INBOARDS_PLOTTED.  Otherwise, define OUTBOARDS_PLOTTED and / or both of them.
    #endif
#endif

#if defined MAGNIFICATION_FACTOR && ( ( PERCENT_OF_LINESPACE_MAGNIFIED_VIEW_SKIPS_WHEN_REPOSITIONED_WHEN_LINESPACE_LIMITS_GET_EXCEEDED > 100 ) || ( PERCENT_OF_LINESPACE_MAGNIFIED_VIEW_SKIPS_WHEN_REPOSITIONED_WHEN_LINESPACE_LIMITS_GET_EXCEEDED < 0 ) )
    #error The macro PERCENT_OF_LINESPACE_MAGNIFIED_VIEW_SKIPS_WHEN_REPOSITIONED_WHEN_LINESPACE_LIMITS_GET_EXCEEDED is out of bounds
#endif

// NOT ALL OF THE FOLLOWING INDEX_OF_INBOARDS_NOT_PLOTTED MACROS WILL BE CORRECT.  ADJUST AS NEEDED DURING DEVELOPMENT
//#error Examine carefully the following calculations:
//The following redefines likely obsolete a number of macro checks in the body of sketch but I haven't gone through to clean them up
#ifdef LM334_BRIDGES
    #if ( 1 > LM334_BRIDGES + 0 ) //This traps both a null and all negatives - they are invalid and get changed to a 1 value, not a 0 value
        #undef LM334_BRIDGES
        #define LM334_BRIDGES 1  //Make sure it contains an integer
        #warning You are specifying LM334_BRIDGES with no number: Assuming 1 for the number of input pairs that the first analog pins form to read analog signals
    #elif ( LM334_BRIDGES == 0 )
        #undef LM334_BRIDGES     //Zero value means same as undefined so undef it to minimize variations
    #endif
    #define TAKE_LEG_VOLTAGE_UP true
    #define TAKE_LEG_VOLTAGE_DOWN false
    #define TIMES_LIMIT ( 3 * DPOT_RATIO )
#endif
#if ( ( ( INBOARDS_PLOTTED < 2 ) && defined SUPERIMPOSE_FIRST_INBOARDS_IN_PAIRS ) || ( defined COMPILE_FOR_DIAGS_ONLY ) )
    #ifdef COMPILE_FOR_DIAGS_ONLY
        #warning You are specifying COMPILE_FOR_DIAGS_ONLY.  If that is not what you want, change that defined macro
        #ifdef LEAVE_POT_VALUES_ALONE_DURING_SETUP
            #undef LEAVE_POT_VALUES_ALONE_DURING_SETUP
        #endif
//        #define INBOARDS_PLOTTED ALL 
//        #define DPOT_LEGS MAX
    #endif
    #undef SUPERIMPOSE_FIRST_INBOARDS_IN_PAIRS
#elif !( defined COMPILE_FOR_DIAGS_ONLY )
    #warning You are not specifying COMPILE_FOR_DIAGS_ONLY.  If that is not what you want, change that defined macro
#endif
#ifdef SUPERIMPOSE_FIRST_INBOARDS_IN_PAIRS
    #if ( 1 > SUPERIMPOSE_FIRST_INBOARDS_IN_PAIRS + 0 ) //This traps both a null and all negatives - they are invalid
        #undef SUPERIMPOSE_FIRST_INBOARDS_IN_PAIRS
        #define SUPERIMPOSE_FIRST_INBOARDS_IN_PAIRS 1
        #warning You are specifying SUPERIMPOSE_FIRST_INBOARDS_IN_PAIRS with no number: Assuming just a single bridge exists
    #elif ( SUPERIMPOSE_FIRST_INBOARDS_IN_PAIRS == 0 )
        #undef SUPERIMPOSE_FIRST_INBOARDS_IN_PAIRS //Zero value means same as undefined so undef it to minimize variations
    #endif
#endif
#define LEGS_PER_DPOT_STYLE_BRIDGE ( 0 )
#define DPOT_LEGS ( 0 )
// always 0 so no macro needed: #define dPotLegMSBusedAndAvailablesIndexLM334_LEG ( 0 )
#define DPOT_LEG_MSB_USED_AND_AVAILABLES_INDEX_BRIDGED_BARE_LEG ( 0 )
#define DPOT_LEG_MSB_USED_AND_AVAILABLES_INDEX_UNBRIDGED_BARE_LEG ( 0 )

#if ( ( defined LM334_BRIDGES ) && ( defined DPOTS_PER_LM334_LEG ) && ( LM334_BRIDGES > 0 ) && ( DPOTS_PER_LM334_LEG > 0 ) )
// Limit checking here for number of DPots this sketch can work with.  Be your own developer and expand this capability to fit your needs
    #if ( ( LM334_BRIDGES > 1 ) || ( DPOTS_PER_LM334_LEG > 3 ) )
        #error To utilize that value for LM334_BRIDGES or DPOTS_PER_LM334_LEG, you will have to develop this sketch further yourself.
    #endif
    #define DPOTS_IN_ALL_LM334_BRIDGES ( LM334_BRIDGES * DPOTS_PER_LM334_LEG * LEGS_PER_DPOT_STYLE_BRIDGE ) //For LM334-tipped bridges //For LM334-tipped bridges
    #define DPOTS_PER_LM334_BRIDGE ( DPOTS_PER_LM334_LEG * LEGS_PER_DPOT_STYLE_BRIDGE )
    #undef LEGS_PER_DPOT_STYLE_BRIDGE
    #define LEGS_PER_DPOT_STYLE_BRIDGE ( 2 )
    #define LM334_BRIDGE_LEGS ( LM334_BRIDGES * LEGS_PER_DPOT_STYLE_BRIDGE )
    #if ( DPOTS_PER_LM334_LEG > 1 )
        #undef DPOT_LEG_MSB_USED_AND_AVAILABLES_INDEX_BRIDGED_BARE_LEG //move where index is for all next styles legs
        #define DPOT_LEG_MSB_USED_AND_AVAILABLES_INDEX_BRIDGED_BARE_LEG ( 2 * LEGS_PER_DPOT_STYLE_BRIDGE * LM334_BRIDGES ) // one member for Total, one for Available for each leg
        #undef DPOT_LEG_MSB_USED_AND_AVAILABLES_INDEX_UNBRIDGED_BARE_LEG //move where index is for next style leg
        #define DPOT_LEG_MSB_USED_AND_AVAILABLES_INDEX_UNBRIDGED_BARE_LEG ( DPOT_LEG_MSB_USED_AND_AVAILABLES_INDEX_BRIDGED_BARE_LEG )
    #endif
#else
    #ifdef DPOTS_PER_LM334_LEG
        #undef DPOTS_PER_LM334_LEG
    #endif
    #define DPOTS_PER_LM334_LEG ( 0 )
    #define LM334_BRIDGES ( 0 )
    #define DPOTS_IN_ALL_LM334_BRIDGES ( 0 ) //For LM334-tipped bridges
    #define LM334_BRIDGE_LEGS ( 0 ) //For LM334-tipped bridges
#endif
#if ( ( defined BARE_DPOT_LEG_BRIDGES ) && ( defined DPOTS_PER_BRIDGED_BARE_LEG ) && ( BARE_DPOT_LEG_BRIDGES > 0 ) && ( DPOTS_PER_BRIDGED_BARE_LEG > 0 ) )
// Limit checking here for number of DPots this sketch can work with.  Be your own developer and expand this capability to fit your needs
    #if ( ( BARE_DPOT_LEG_BRIDGES > 0 ) || ( DPOTS_PER_BRIDGED_BARE_LEG > 0 ) )
        #error To utilize that value for BARE_DPOT_LEG_BRIDGES or DPOTS_PER_BRIDGED_BARE_LEG, you will have to develop this sketch version further yourself.
    #endif
    #define DPOTS_IN_ALL_BARE_LEG_BRIDGES ( BARE_DPOT_LEG_BRIDGES * DPOTS_PER_BRIDGED_BARE_LEG * LEGS_PER_DPOT_STYLE_BRIDGE ) //for bare DPot bridges
    #define DPOTS_PER_BARE_LEG_BRIDGE ( DPOTS_PER_BRIDGED_BARE_LEG * LEGS_PER_DPOT_STYLE_BRIDGE )
    #undef LEGS_PER_DPOT_STYLE_BRIDGE
    #define LEGS_PER_DPOT_STYLE_BRIDGE ( 2 )
    #define BARE_BRIDGE_LEGS ( BARE_DPOT_LEG_BRIDGES * LEGS_PER_DPOT_STYLE_BRIDGE ) //for bare DPot bridges
    #if ( DPOTS_PER_BRIDGED_BARE_LEG > 1 )
        #undef DPOT_LEG_MSB_USED_AND_AVAILABLES_INDEX_UNBRIDGED_BARE_LEG //move where index is for next style leg
        #define DPOT_LEG_MSB_USED_AND_AVAILABLES_INDEX_UNBRIDGED_BARE_LEG ( DPOT_LEG_MSB_USED_AND_AVAILABLES_INDEX_BRIDGED_BARE_LEG + ( 2 * LEGS_PER_DPOT_STYLE_BRIDGE * BARE_DPOT_LEG_BRIDGES ) ) // one member for Total, one for Available for each leg
    #endif
#else
    #ifdef DPOTS_PER_BRIDGED_BARE_LEG
        #undef DPOTS_PER_BRIDGED_BARE_LEG
    #endif
    #define BARE_DPOT_LEG_BRIDGES ( 0 )
    #define DPOTS_PER_BRIDGED_BARE_LEG ( 0 )
    #define DPOTS_IN_ALL_BARE_LEG_BRIDGES ( 0 ) //for bare DPot bridges
    #define BARE_BRIDGE_LEGS ( 0 ) //for bare DPot bridges
#endif

#if ( ( defined BARE_DPOT_LEGS_UNBRIDGED ) && ( defined DPOTS_PER_UNBRIDGED_BARE_LEG ) && ( BARE_DPOT_LEGS_UNBRIDGED > 0 ) && ( DPOTS_PER_UNBRIDGED_BARE_LEG > 0 ) )
// Limit checking here for number of DPots this sketch can work with.  Be your own developer and expand this capability to fit your needs
    #if ( ( DPOTS_IN_ALL_BARE_LEGS_UNBRIDGED > 0 ) || ( BARE_DPOT_LEGS_UNBRIDGED > 0 ) )
        #error To utilize that value for LM334_BRIDGES or DPOTS_PER_LM334_LEG, you will have to develop this sketch version further yourself.
    #endif
    #define DPOTS_IN_ALL_BARE_LEGS_UNBRIDGED ( BARE_DPOT_LEGS_UNBRIDGED * DPOTS_PER_UNBRIDGED_BARE_LEG ) //FUTURE USE for unbridged DPot control
#else
    #ifdef DPOTS_PER_UNBRIDGED_BARE_LEG
        #undef DPOTS_PER_UNBRIDGED_BARE_LEG
    #endif
    #ifdef BARE_DPOT_LEGS_UNBRIDGED
        #undef BARE_DPOT_LEGS_UNBRIDGED
    #endif
    #define DPOTS_PER_UNBRIDGED_BARE_LEG ( 0 )
    #define DPOTS_IN_ALL_BARE_LEGS_UNBRIDGED ( 0 ) //FUTURE USE for unbridged DPot control
    #define BARE_DPOT_LEGS_UNBRIDGED ( 0 )
#endif
//#if ( ( LM334_BRIDGES + BARE_DPOT_LEG_BRIDGES /*+ BARE_DPOT_LEGS_UNBRIDGED*/ ) > OUTBOARDS_PLOTTED )
//Notice that BARE_DPOT_LEGS_UNBRIDGED is a don't care to allow greatest user flexibility
//#error The number of outboard ADCs is not adequate for the total from the specified values of LM334_BRIDGES + BARE_DPOT_LEG_BRIDGES 
//#endif
#ifdef DPOT_LEGS
    #undef DPOT_LEGS
#endif
#define DPOT_LEGS ( LM334_BRIDGE_LEGS + BARE_BRIDGE_LEGS + BARE_DPOT_LEGS_UNBRIDGED )
#if ( DPOTS_IN_ALL_LM334_BRIDGES + DPOTS_IN_ALL_BARE_LEG_BRIDGES == 0 )
    #undef LEGS_PER_DPOT_STYLE_BRIDGE //Means there are no bridges with DPots in them
    #undef AUTO_BRIDGE_BALANCING
#endif
#if ( DPOT_LEGS == 0 )
//
//Here means there are no DPots in the system anywhere
//
    #undef INJECT_DIAGNOSTIC_SQUARE_WAVE_ON_SIGNAL_PIN_OF_SPECIFIED_OUTBOARD_ADC
    #undef INJECT_DIAGNOSTIC_SQUARE_WAVE_ON_REFERENCE_PIN_OF_SPECIFIED_OUTBOARD_ADC
    #undef TEST_STEP_UP_DOWN
#else
/*
  Using a Microchip MCP4162 digital potentiometer
    [http://bit.ly/iwDmnd]
    http://tronixstuff.com/tutorials > chapter 34 | CC by-sa-nc | John Boxall
    SS – digital 10 to CS of a single digital pot, not abstracted by library call, so can be any pin as determined within main function unidirectional NOT PIN 10 ON LEONARDO - IS FOUND ON LED_BUILTIN_RX (PIN 17) ONLY
    MOSI – digital 11 to inputs of all digital pots unidirectional NOT PIN 11 ON LEONARDO - IS FOUND ON 1CSP ONLY.  REQ'D IN ALL CASES.
    MISO – digital 12 to outputs of all digital pots unidirectional NOT PIN 12 ON LEONARDO - IS FOUND ON 1CSP ONLY.  REQ'D IN SD CARD. OPTIONAL WHEN DPOTS AREN'T SUPPLIED WITH 8.5-12 VDC FOR PERSISTENCE.
    SCK – digital 13 to CLK of all digital pots unidirectional NOT PIN 13 ON LEONARDO - IS FOUND ON 1CSP ONLY
    Clock speed of MCP4162 is 10 MHz max, well capable to use default Arduino speed of 4 MHz.
    EEPROM and nonvolatile settings are only available with >8.5 Vdc to <12.5Vdc applied to CS pins of MCP4162, which we don't have.
    Therefore, we have no need to read data back from digipots b/c we're storing their settings in sketch variables.
*/
    #ifndef SPIINCLUDED
        #include "SPI.h" //This is the hardware implementation of SPI with CS pin addressable devices (instead of devices with unidirectional data in and data out pins needing addressed via data).  The software implementation uses shiftIn() instead and is slower but frees up otherwise-CS pins and can be used adjunctive for cases where a chip has no CS pin.  Adafruit_ADS1015 uses the shiftIn() method, so those pins are user's choice.  Not data addressable as would be in I2C
        #define SPIINCLUDED
    #endif
    #ifdef INJECT_DIAGNOSTIC_SQUARE_WAVE_ON_SIGNAL_PIN_OF_SPECIFIED_OUTBOARD_ADC
        #if ( 1 > INJECT_DIAGNOSTIC_SQUARE_WAVE_ON_SIGNAL_PIN_OF_SPECIFIED_OUTBOARD_ADC + 0 )
            #undef INJECT_DIAGNOSTIC_SQUARE_WAVE_ON_SIGNAL_PIN_OF_SPECIFIED_OUTBOARD_ADC
            #define INJECT_DIAGNOSTIC_SQUARE_WAVE_ON_SIGNAL_PIN_OF_SPECIFIED_OUTBOARD_ADC 0 //make sure it contains a bridge index or leg for non-bridged legs, default is bridge 0
        #endif
    #endif
    #ifdef INJECT_DIAGNOSTIC_SQUARE_WAVE_ON_REFERENCE_PIN_OF_SPECIFIED_OUTBOARD_ADC
        #if ( 1 > INJECT_DIAGNOSTIC_SQUARE_WAVE_ON_REFERENCE_PIN_OF_SPECIFIED_OUTBOARD_ADC + 0 )
            #undef INJECT_DIAGNOSTIC_SQUARE_WAVE_ON_REFERENCE_PIN_OF_SPECIFIED_OUTBOARD_ADC
            #define INJECT_DIAGNOSTIC_SQUARE_WAVE_ON_REFERENCE_PIN_OF_SPECIFIED_OUTBOARD_ADC 0 //make sure it contains a bridge index or leg for non-bridged legs, default is bridge 0
        #endif
    #endif

    #define DPOTS ( DPOTS_IN_ALL_LM334_BRIDGES + DPOTS_IN_ALL_BARE_LEG_BRIDGES + DPOTS_IN_ALL_BARE_LEGS_UNBRIDGED )
    #define READ_AND_PLOT_IN_EACH_LAP true
    #define WORK_ON_THE_REFERENCE_LEG true
/*
      The following are globals since their contents can only be calculated at run-time and necessarily must remain accessible by every function without loss or recalculation, or are essential to the calculation of another global
      and we don't want to waste the CPU time of making them into preprocessor macros which would get calculated every single time the macro is used instead of just a single time when the DPotLeg of interest is changed
*/
    //The following variable is intended to be stored in EEPROM once calculated
    #define NUM_ELEMENTS_PER_LEG_IN_dPotLegMSBusedAndAvailables_ARRAY 2 //one for total in use, one for available
    static uint16_t dPotLegMSBusedAndAvailables[ NUM_ELEMENTS_PER_LEG_IN_dPotLegMSBusedAndAvailables_ARRAY * DPOT_LEGS ]; //This will only be needed on legs with > 1 Dpots: each leg can store totalAllMSBsThisLeg availableAllMSBsThisLeg
//Since the following defines take up no space in compiled rendering unless they get used, leave them here even if never used
    #define MSB_SETTINGS_TOTAL_THIS_LEG( dPotLeg )                         ( dPotLegMSBusedAndAvailables[   NUM_ELEMENTS_PER_LEG_IN_dPotLegMSBusedAndAvailables_ARRAY * dPotLeg      ] )
    #define MSB_SETTINGS_AVAILABLE_THIS_LEG( dPotLeg )                     ( dPotLegMSBusedAndAvailables[ ( NUM_ELEMENTS_PER_LEG_IN_dPotLegMSBusedAndAvailables_ARRAY * dPotLeg ) + 1 ] )
    #define MSB_SETTINGS_TOTAL_REFERENCE_TO_THIS_SIGNAL_LEG( dPotLeg )     ( dPotLegMSBusedAndAvailables[ ( dPotLeg < ( LM334_BRIDGE_LEGS + BARE_BRIDGE_LEGS ) ) ? ( ( NUM_ELEMENTS_PER_LEG_IN_dPotLegMSBusedAndAvailables_ARRAY * dPotLeg ) + 2 ) : ( NUM_ELEMENTS_PER_LEG_IN_dPotLegMSBusedAndAvailables_ARRAY * dPotLeg ) ] )
    #define MSB_SETTINGS_AVAILABLE_REFERENCE_TO_THIS_SIGNAL_LEG( dPotLeg ) ( dPotLegMSBusedAndAvailables[ ( dPotLeg < ( LM334_BRIDGE_LEGS + BARE_BRIDGE_LEGS ) ) ? ( ( NUM_ELEMENTS_PER_LEG_IN_dPotLegMSBusedAndAvailables_ARRAY * dPotLeg ) + 3 ) : ( ( NUM_ELEMENTS_PER_LEG_IN_dPotLegMSBusedAndAvailables_ARRAY * dPotLeg ) + 1 ) ] )

    #define MSB_SETTINGS_TOTAL_SIGNAL_THIS_BRIDGE( bridge )        ( dPotLegMSBusedAndAvailables[ bridge < ( LM334_BRIDGES + BARE_DPOT_LEG_BRIDGES ) ?   NUM_ELEMENTS_PER_LEG_IN_dPotLegMSBusedAndAvailables_ARRAY * bridge * LEGS_PER_DPOT_STYLE_BRIDGE       : ( ( ( LM334_BRIDGES + BARE_DPOT_LEG_BRIDGES ) * LEGS_PER_DPOT_STYLE_BRIDGE * NUM_ELEMENTS_PER_LEG_IN_dPotLegMSBusedAndAvailables_ARRAY ) + ( NUM_ELEMENTS_PER_LEG_IN_dPotLegMSBusedAndAvailables_ARRAY * ( bridge - ( LM334_BRIDGES + BARE_DPOT_LEG_BRIDGES ) ) ) )    ] )
    #define MSB_SETTINGS_AVAILABLE_SIGNAL_THIS_BRIDGE( bridge )    ( dPotLegMSBusedAndAvailables[ bridge < ( LM334_BRIDGES + BARE_DPOT_LEG_BRIDGES ) ? ( NUM_ELEMENTS_PER_LEG_IN_dPotLegMSBusedAndAvailables_ARRAY * bridge * LEGS_PER_DPOT_STYLE_BRIDGE ) + 1 : ( ( ( LM334_BRIDGES + BARE_DPOT_LEG_BRIDGES ) * LEGS_PER_DPOT_STYLE_BRIDGE * NUM_ELEMENTS_PER_LEG_IN_dPotLegMSBusedAndAvailables_ARRAY ) + ( NUM_ELEMENTS_PER_LEG_IN_dPotLegMSBusedAndAvailables_ARRAY * ( bridge - ( LM334_BRIDGES + BARE_DPOT_LEG_BRIDGES ) ) ) + 1 ) ] )
    #define MSB_SETTINGS_TOTAL_REFERENCE_THIS_BRIDGE( bridge )     ( dPotLegMSBusedAndAvailables[ bridge < ( LM334_BRIDGES + BARE_DPOT_LEG_BRIDGES ) ? ( NUM_ELEMENTS_PER_LEG_IN_dPotLegMSBusedAndAvailables_ARRAY * bridge * LEGS_PER_DPOT_STYLE_BRIDGE ) + 2 : ( ( ( LM334_BRIDGES + BARE_DPOT_LEG_BRIDGES ) * LEGS_PER_DPOT_STYLE_BRIDGE * NUM_ELEMENTS_PER_LEG_IN_dPotLegMSBusedAndAvailables_ARRAY ) + ( NUM_ELEMENTS_PER_LEG_IN_dPotLegMSBusedAndAvailables_ARRAY * ( bridge - ( LM334_BRIDGES + BARE_DPOT_LEG_BRIDGES ) ) ) )    ] )
    #define MSB_SETTINGS_AVAILABLE_REFERENCE_THIS_BRIDGE( bridge ) ( dPotLegMSBusedAndAvailables[ bridge < ( LM334_BRIDGES + BARE_DPOT_LEG_BRIDGES ) ? ( NUM_ELEMENTS_PER_LEG_IN_dPotLegMSBusedAndAvailables_ARRAY * bridge * LEGS_PER_DPOT_STYLE_BRIDGE ) + 3 : ( ( ( LM334_BRIDGES + BARE_DPOT_LEG_BRIDGES ) * LEGS_PER_DPOT_STYLE_BRIDGE * NUM_ELEMENTS_PER_LEG_IN_dPotLegMSBusedAndAvailables_ARRAY ) + ( NUM_ELEMENTS_PER_LEG_IN_dPotLegMSBusedAndAvailables_ARRAY * ( bridge - ( LM334_BRIDGES + BARE_DPOT_LEG_BRIDGES ) ) ) + 1 ) ] )

/*
    WHY WE DON'T GLOBALLY STORE THE BRIDGE IN CONTEXT LIKE WE DO THESE OTHER VARS:
    Because sending the bridge as an argument instead is never inconvenient as
    it is always handy from where functions are called that need to know it.
    These globals are here b/c otherwise they would have to be recalculated
    multiple times within the same bridge or leg context or else clutter 
    function argument lists into too much ugliness.  Not so with bridge.
*/
    static uint16_t tattoo = 0;
    static uint8_t whichBridgeOrOutboardADCindex = 0;
    static uint16_t indexOfThisDPotCSpinInDPotArrays = 0;
    static uint8_t dPotLeg;
    static uint8_t dPotsPerThisLeg;
    static uint8_t dPotsPerThisBridge;
    static uint8_t mSBgroupSize;
    static uint8_t lSBdPotIndexThisLeg;
    static uint8_t lSBdPotIndexThisLegReference;
    static uint8_t referenceLSBdPotIndexThisBridge;
    static uint8_t firstMSBindexThisLeg;
    static uint8_t firstMSBindexThisLegReference;
    static uint8_t firstReferenceMSBindexThisBridge;
#ifdef __LGT8FX8E__
void EEPROMupdate ( unsigned long address, u8 val )
{
    if( EEPROM.read( address ) != val ) EEPROM.write( address, val );
}
#endif
    static uint8_t whatIsSignalLegThisBridge( uint8_t bridge )
    {
        return ( ( whichBridgeOrOutboardADCindex < ( LM334_BRIDGES + BARE_BRIDGE_LEGS ) ) ? \
        ( whichBridgeOrOutboardADCindex * 2 ) : \
        ( LM334_BRIDGE_LEGS + BARE_BRIDGE_LEGS + whichBridgeOrOutboardADCindex - ( LM334_BRIDGES + BARE_BRIDGE_LEGS ) ) );
    }
    uint8_t whatIsBridgeOfThisDPotLeg( uint8_t dPotLeg )
    { //returns the value of whichBridgeOrOutboardADCindex
        return ( dPotLeg < ( LM334_BRIDGE_LEGS + BARE_BRIDGE_LEGS ) ? \
        dPotLeg >> 1 : ( LM334_BRIDGES + BARE_DPOT_LEG_BRIDGES + dPotLeg - ( LM334_BRIDGE_LEGS + BARE_BRIDGE_LEGS ) ) );
    }
    uint8_t whatIsDPotsPerThisLeg( uint8_t dPotLeg )
    { //returns the value of dPotsPerThisLeg
        return ( dPotLeg < LM334_BRIDGE_LEGS ? \
                DPOTS_PER_LM334_LEG : \
                ( dPotLeg < ( LM334_BRIDGE_LEGS + BARE_BRIDGE_LEGS ) ) ? \
                DPOTS_PER_BRIDGED_BARE_LEG : \
                DPOTS_PER_UNBRIDGED_BARE_LEG );
    }
    uint8_t whatIsDPotsPerThisBridge( uint8_t whichBridgeOrOutboardADCindex )
    { //returns the value of dPotsPerThisBridge
        return ( whichBridgeOrOutboardADCindex < LM334_BRIDGES ? \
                ( DPOTS_PER_LM334_LEG << 1 ) : \
                ( whichBridgeOrOutboardADCindex < ( LM334_BRIDGES + BARE_DPOT_LEG_BRIDGES ) ? \
                ( DPOTS_PER_BRIDGED_BARE_LEG << 1 ) : \
                DPOTS_PER_UNBRIDGED_BARE_LEG ) );
    }
    uint8_t whatIsMSBgroupSizeInThisDPotLeg( uint8_t dPotLeg )
    { //returns the value of mSBgroupSize
        return ( dPotLeg < LM334_BRIDGE_LEGS ? \
                ( DPOTS_PER_LM334_LEG > 2 ? ( DPOTS_PER_LM334_LEG - 1 ): 1 ): \
                ( dPotLeg < ( LM334_BRIDGE_LEGS + BARE_BRIDGE_LEGS ) ? \
                ( DPOTS_PER_BRIDGED_BARE_LEG > 2 ? ( DPOTS_PER_BRIDGED_BARE_LEG - 1 ): 1 ): \
                ( DPOTS_PER_UNBRIDGED_BARE_LEG > 2 ? ( DPOTS_PER_UNBRIDGED_BARE_LEG - 1 ) : 1 ) ) );
    }
    uint8_t whatIsMSBgroupSizeInThisBridge( uint8_t whichBridgeOrOutboardADCindex )
    { //returns the value of mSBgroupSize
        return ( whichBridgeOrOutboardADCindex < LM334_BRIDGES ? \
                ( DPOTS_PER_LM334_LEG > 2 ? ( DPOTS_PER_LM334_LEG - 1 ): 1 ): \
                ( whichBridgeOrOutboardADCindex < ( LM334_BRIDGES + BARE_DPOT_LEG_BRIDGES ) ? \
                ( DPOTS_PER_BRIDGED_BARE_LEG > 2 ? ( DPOTS_PER_BRIDGED_BARE_LEG - 1 ): 1 ): \
                ( DPOTS_PER_UNBRIDGED_BARE_LEG > 2 ? ( DPOTS_PER_UNBRIDGED_BARE_LEG - 1 ) : 1 ) ) );
    }
    uint8_t whatIsLSBdPotIndexThisLeg( uint8_t dPotLeg )
    { //returns the value of lSBdPotIndexThisLeg
        return ( dPotLeg < LM334_BRIDGE_LEGS ? \
                ( dPotLeg * DPOTS_PER_LM334_LEG ) : \
                ( dPotLeg < ( LM334_BRIDGE_LEGS + BARE_BRIDGE_LEGS ) ) ? \
                ( DPOTS_IN_ALL_LM334_BRIDGES + ( ( dPotLeg - LM334_BRIDGE_LEGS ) * DPOTS_PER_BRIDGED_BARE_LEG ) ) : \
                ( DPOTS_IN_ALL_LM334_BRIDGES + DPOTS_IN_ALL_BARE_LEG_BRIDGES + ( ( dPotLeg - ( LM334_BRIDGE_LEGS + DPOTS_IN_ALL_BARE_LEG_BRIDGES ) * DPOTS_PER_UNBRIDGED_BARE_LEG ) ) ) );
    }
    uint8_t whatIsSignalLSBdPotIndexThisBridge( uint8_t whichBridgeOrOutboardADCindex )
    { //returns the value of lSBdPotIndexThisLeg
        return ( whichBridgeOrOutboardADCindex < LM334_BRIDGES ? \
                ( whichBridgeOrOutboardADCindex * DPOTS_PER_LM334_LEG * LEGS_PER_DPOT_STYLE_BRIDGE ) : \
                ( whichBridgeOrOutboardADCindex < ( LM334_BRIDGES + BARE_DPOT_LEG_BRIDGES ) ? \
                ( DPOTS_IN_ALL_LM334_BRIDGES + ( ( ( whichBridgeOrOutboardADCindex - LM334_BRIDGES ) * LEGS_PER_DPOT_STYLE_BRIDGE ) * DPOTS_PER_BRIDGED_BARE_LEG ) ) : \
                ( DPOTS_IN_ALL_LM334_BRIDGES + DPOTS_IN_ALL_BARE_LEG_BRIDGES + ( ( ( whichBridgeOrOutboardADCindex - ( LM334_BRIDGES + BARE_DPOT_LEG_BRIDGES ) ) * LEGS_PER_DPOT_STYLE_BRIDGE ) * DPOTS_PER_UNBRIDGED_BARE_LEG ) ) ) );
    }
    uint8_t whatIsReferenceLSBdPotIndexThisBridge255IfNone( uint8_t whichBridgeOrOutboardADCindex )
    { //returns the value of lSBdPotIndexThisLeg
        return ( whichBridgeOrOutboardADCindex < LM334_BRIDGES ? \
                ( ( whichBridgeOrOutboardADCindex * DPOTS_PER_LM334_LEG * LEGS_PER_DPOT_STYLE_BRIDGE ) + DPOTS_PER_LM334_LEG ): \
                ( whichBridgeOrOutboardADCindex < ( LM334_BRIDGES + BARE_DPOT_LEG_BRIDGES ) ? \
                ( ( DPOTS_IN_ALL_LM334_BRIDGES + ( ( ( whichBridgeOrOutboardADCindex - LM334_BRIDGES ) * LEGS_PER_DPOT_STYLE_BRIDGE ) * DPOTS_PER_BRIDGED_BARE_LEG ) ) + DPOTS_PER_BRIDGED_BARE_LEG ) : \
                255 /*special value for whenever there isn't even a reference leg in this bridge, let alone such a DPot*/) );
    }
    uint8_t whatIsFirstMSBindexThisLeg( uint8_t dPotLeg )
    {
        return ( dPotLeg < LM334_BRIDGE_LEGS ? \
                ( dPotLeg * DPOTS_PER_LM334_LEG ) + ( ( DPOTS_PER_LM334_LEG > 1 ) ? 1 : 0 ) : \
                ( dPotLeg < ( LM334_BRIDGE_LEGS + BARE_BRIDGE_LEGS ) ) ? \
                ( DPOTS_IN_ALL_LM334_BRIDGES + ( ( dPotLeg - LM334_BRIDGE_LEGS ) * DPOTS_PER_BRIDGED_BARE_LEG ) + ( ( DPOTS_PER_BRIDGED_BARE_LEG > 1 ) ? 1 : 0 ) ) : \
                ( DPOTS_IN_ALL_LM334_BRIDGES + DPOTS_IN_ALL_BARE_LEG_BRIDGES + ( ( dPotLeg - ( LM334_BRIDGE_LEGS + DPOTS_IN_ALL_BARE_LEG_BRIDGES ) * DPOTS_PER_UNBRIDGED_BARE_LEG ) ) + ( ( DPOTS_PER_UNBRIDGED_BARE_LEG > 1 ) ? 1 : 0 ) ) );
    }
    uint8_t whatIsFirstSignalMSBindexThisBridge( uint8_t whichBridgeOrOutboardADCindex )
    {
        return ( whichBridgeOrOutboardADCindex < LM334_BRIDGES ? \
                ( whichBridgeOrOutboardADCindex * DPOTS_PER_LM334_LEG * LEGS_PER_DPOT_STYLE_BRIDGE ) + ( ( DPOTS_PER_LM334_LEG > 1 ) ? 1 : 0 ) : \
                ( whichBridgeOrOutboardADCindex < ( LM334_BRIDGES + BARE_DPOT_LEG_BRIDGES ) ? \
                ( DPOTS_IN_ALL_LM334_BRIDGES + ( ( ( whichBridgeOrOutboardADCindex - LM334_BRIDGES ) * LEGS_PER_DPOT_STYLE_BRIDGE ) * DPOTS_PER_BRIDGED_BARE_LEG ) + ( ( DPOTS_PER_BRIDGED_BARE_LEG > 1 ) ? 1 : 0 ) ) : \
                ( DPOTS_IN_ALL_LM334_BRIDGES + DPOTS_IN_ALL_BARE_LEG_BRIDGES + ( ( ( whichBridgeOrOutboardADCindex - ( LM334_BRIDGES + BARE_DPOT_LEG_BRIDGES ) ) * LEGS_PER_DPOT_STYLE_BRIDGE ) * DPOTS_PER_UNBRIDGED_BARE_LEG ) + ( ( DPOTS_PER_UNBRIDGED_BARE_LEG > 1 ) ? 1 : 0 ) ) ) );
    } 
    uint8_t whatIsFirstReferenceMSBindexThisBridge255IfNone( uint8_t whichBridgeOrOutboardADCindex )
    {
        return ( whichBridgeOrOutboardADCindex < LM334_BRIDGES ? \
                ( ( whichBridgeOrOutboardADCindex * DPOTS_PER_LM334_LEG * LEGS_PER_DPOT_STYLE_BRIDGE ) + DPOTS_PER_LM334_LEG + ( ( DPOTS_PER_LM334_LEG > 1 ) ? 1 : 0 ) ): \
                ( whichBridgeOrOutboardADCindex < ( LM334_BRIDGES + BARE_DPOT_LEG_BRIDGES ) ? \
                ( ( DPOTS_IN_ALL_LM334_BRIDGES + ( ( ( whichBridgeOrOutboardADCindex - LM334_BRIDGES ) * LEGS_PER_DPOT_STYLE_BRIDGE ) * DPOTS_PER_BRIDGED_BARE_LEG ) ) + DPOTS_PER_BRIDGED_BARE_LEG + ( ( DPOTS_PER_BRIDGED_BARE_LEG > 1 ) ? 1 : 0 ) ) : \
                255 /*special value for whenever there isn't even a reference leg in this bridge, let alone such a DPot*/) );
    }
    void configureFromDPotLeg( void ) //Note that the way the dPotPins array is ordered allows the following to work even with unbridged legs in the system
    { //checking whether this got executed for the signal leg when the current context is for the reference leg: indexOfThisDPotCSpinInDPotArrays < lSBdPotInLegReference ? <signal leg value> : <reference leg value>
    //If the leg has only a single DPot, the mSBgroupSize will be one and both lSBdPotIndexThisLeg and firstMSBindexThisLeg will equate as firstDPotInLeg in signal leg - the reference leg acts similarly.
        dPotsPerThisLeg = whatIsDPotsPerThisLeg( dPotLeg );
        dPotsPerThisBridge = whatIsDPotsPerThisBridge( whatIsBridgeOfThisDPotLeg( dPotLeg ) );
        
        mSBgroupSize = whatIsMSBgroupSizeInThisBridge( whatIsBridgeOfThisDPotLeg( dPotLeg ) );
        
        lSBdPotIndexThisLeg = whatIsLSBdPotIndexThisLeg( dPotLeg );
        lSBdPotIndexThisLegReference = ( dPotLeg < ( LM334_BRIDGE_LEGS + BARE_BRIDGE_LEGS ) ) ? lSBdPotIndexThisLeg + dPotsPerThisLeg : lSBdPotIndexThisLeg;
        referenceLSBdPotIndexThisBridge = whatIsReferenceLSBdPotIndexThisBridge255IfNone( whichBridgeOrOutboardADCindex );
        
        firstMSBindexThisLeg = lSBdPotIndexThisLeg + ( ( dPotsPerThisLeg > 1 ) ? 1 : 0 );
        firstMSBindexThisLegReference = ( dPotLeg < ( LM334_BRIDGE_LEGS + BARE_BRIDGE_LEGS ) ) ? firstMSBindexThisLeg + dPotsPerThisLeg : firstMSBindexThisLeg;
        firstReferenceMSBindexThisBridge = whatIsFirstReferenceMSBindexThisBridge255IfNone( whichBridgeOrOutboardADCindex );
    }
    
    void configureFromDPotIndex()
    {
      dPotLeg = indexOfThisDPotCSpinInDPotArrays < DPOTS_IN_ALL_LM334_BRIDGES ? \
                ( indexOfThisDPotCSpinInDPotArrays / DPOTS_PER_LM334_LEG ) : \
                indexOfThisDPotCSpinInDPotArrays < DPOTS_IN_ALL_LM334_BRIDGES + DPOTS_IN_ALL_BARE_LEG_BRIDGES ? \
                ( LM334_BRIDGE_LEGS + ( ( indexOfThisDPotCSpinInDPotArrays - DPOTS_IN_ALL_LM334_BRIDGES ) / DPOTS_PER_BRIDGED_BARE_LEG ) ) : \
                LM334_BRIDGE_LEGS + BARE_BRIDGE_LEGS + ( ( indexOfThisDPotCSpinInDPotArrays - ( LM334_BRIDGE_LEGS + BARE_BRIDGE_LEGS ) ) / DPOTS_IN_ALL_BARE_LEGS_UNBRIDGED );
      configureFromDPotLeg();
    }
    
    void configureForSignalLegWithBridgeIndexIncludingNonBridgedLegs( uint8_t bridge )
    {
        whichBridgeOrOutboardADCindex = bridge;
      dPotLeg = ( whichBridgeOrOutboardADCindex < LM334_BRIDGES + BARE_DPOT_LEG_BRIDGES ) ? ( whichBridgeOrOutboardADCindex * LEGS_PER_DPOT_STYLE_BRIDGE ) :  \
      ( ( ( LM334_BRIDGES + BARE_DPOT_LEG_BRIDGES ) * LEGS_PER_DPOT_STYLE_BRIDGE ) + ( whichBridgeOrOutboardADCindex - ( LM334_BRIDGES + BARE_DPOT_LEG_BRIDGES ) ) );
      configureFromDPotLeg();
    }
    
    void configureForReferenceLegWithBridgeIndex( uint8_t bridge )
    { //Not using configureForSignalLegWithBridgeIndexIncludingNonBridgedLegs b/c would be too wasteful of CPU
        whichBridgeOrOutboardADCindex = bridge;
      dPotLeg = ( whichBridgeOrOutboardADCindex < LM334_BRIDGES + BARE_DPOT_LEG_BRIDGES ) ? ( ( whichBridgeOrOutboardADCindex * LEGS_PER_DPOT_STYLE_BRIDGE ) + 1 ) :  \
      ( ( ( LM334_BRIDGES + BARE_DPOT_LEG_BRIDGES ) * LEGS_PER_DPOT_STYLE_BRIDGE ) + ( whichBridgeOrOutboardADCindex - ( LM334_BRIDGES + BARE_DPOT_LEG_BRIDGES ) ) );
      configureFromDPotLeg();
    }
    #define MAX_DPOT_SETTG ( signed )256 //This settingValue is 1 less than the actual number of steps b/c the lowest setting is 0 - zero indexed, but since it equates to practical zero resistance this works fine
    
    //    #if ( LM334_BRIDGES > 0 ) Just b/c this conforms to the pattern
    //When using one or two 3:8 decoders, note that these pins numbers must be greater than 127
    //Never use bit 6 of DPotPin for anything except to designate the second pot in a dual pkg
    /*
        To scale up to multiple values of digipotsperleg:
      x1   fix LSB_DPOT_B0U4_PIN names and such
      x2   fix index order within DPotSettings and DPotPins
      >3   fix LSB_DPOT_B0SIG_STARTVALUE names and such
      4   fix DPOT_RATIO to something that will work where it is used
      5
      Never use bit 6 of DPotPin for anything except to designate the second pot in a dual pkg
    
    */
    //If a digipot is the second in a MCP42xx pkg, you will OR that digipot's pin number with B01000000 (add 64) like so: #define LSB_DPOT_B0U4_PIN ( 7 + 64 ) would be for when pin 7 is the physical Arduino Digital pin.  MCP41xx packages need no such consideration
    //If you find that you don't understand that, I'd encourage you to learn the topics of converting between hexadecimal, decimal, and binary and to learn bitwise boolean operations
    #define LSB_DPOT_B0SIG_PIN ( 8 + 64 )         //U8-1 Signal LSB fine adjust digital pot's CS line connected to here
//    #define LSB_DPOT_B0SIG_STARTVALUE 0 //309 52 - 54 or ( MAX_DPOT_SETTG / 2 )   //this settingValue in digipots and with 1 MOhm resistors for the LM334 loads put the LM334 output voltage at closest: with three DPots per leg
    #define LSB_DPOT_B0SIG_STARTVALUE 0 //304 52 - 54 or ( MAX_DPOT_SETTG / 2 )   //this settingValue in digipots and with 1 MOhm resistors for the LM334 loads put the LM334 output voltage at closest: with three DPots per leg
//    #define LSB_DPOT_B0SIG_STARTVALUE 83 //52 - 54 or ( MAX_DPOT_SETTG / 2 )   //this settingValue in digipots and with 1 MOhm resistors for the LM334 loads put the LM334 output voltage at closest: with three DPots per leg
    
    #if ( ( DPOTS_PER_LM334_LEG > 0 ) || ( DPOTS_PER_BRIDGED_BARE_LEG > 0 ) )
        #define LSB_DPOT_B0REF_PIN 8        //U8-0 Reference LSB fine adjust digital pot's CS line connected to here
//        #define LSB_DPOT_B0REF_STARTVALUE 0 //310 or ( MAX_DPOT_SETTG / 2 )   //this settingValue in digipots and with 1 MOhm resistors for the LM334 loads put the LM334 output voltage at closest: with three DPots per leg
        #define LSB_DPOT_B0REF_STARTVALUE 0 //305 or ( MAX_DPOT_SETTG / 2 )   //this settingValue in digipots and with 1 MOhm resistors for the LM334 loads put the LM334 output voltage at closest: with three DPots per leg
//        #define LSB_DPOT_B0REF_STARTVALUE 87 //or ( MAX_DPOT_SETTG / 2 )   //this settingValue in digipots and with 1 MOhm resistors for the LM334 loads put the LM334 output voltage at closest: with three DPots per leg
    //        #define LSB_DPOT_B0REF_STARTVALUE 18 //or ( MAX_DPOT_SETTG / 2 )   //this settingValue in digipots and with 1 MOhm resistors for the LM334 loads put the LM334 output voltage at closest: with two DPots per leg
    #endif
    #if ( ( DPOTS_PER_LM334_LEG > 1 ) || ( DPOTS_PER_BRIDGED_BARE_LEG > 1 ) || ( DPOTS_PER_UNBRIDGED_BARE_LEG > 1 ) )
        #define NON_LSB_DPOT_1_B0SIG_PIN ( 7 + 64 )          //U7-1 MSB digital pot of signal leg CS line connected to here.  coarse adjust B positive (signal) leg
//        #define NON_LSB_DPOT_1_B0SIG_STARTVALUE ( MAX_DPOT_SETTG / 4 ) //or ( MAX_DPOT_SETTG / 2 )  //this settingValue in digipots and with 1 MOhm resistors for the LM334 loads put the LM334 output voltage at closest: with two or three DPots per leg
        #define NON_LSB_DPOT_1_B0SIG_STARTVALUE 255 //or ( MAX_DPOT_SETTG / 2 )  //this settingValue in digipots and with 1 MOhm resistors for the LM334 loads put the LM334 output voltage at closest: with two or three DPots per leg
    #endif
    #if ( ( DPOTS_PER_LM334_LEG > 1 ) || ( DPOTS_PER_BRIDGED_BARE_LEG > 1 ) )
        #define NON_LSB_DPOT_1_B0REF_PIN 7         //U7-0 MSB digital pot of reference leg CS line connected to here.  coarse adjust B negative (reference) leg
//        #define NON_LSB_DPOT_1_B0REF_STARTVALUE ( MAX_DPOT_SETTG / 4 ) //or ( MAX_DPOT_SETTG / 2 )   //this settingValue in digipots and with 1 MOhm resistors for the LM334 loads put the LM334 output voltage at closest: with three DPots per leg
        #define NON_LSB_DPOT_1_B0REF_STARTVALUE 0 //or ( MAX_DPOT_SETTG / 2 )   //this settingValue in digipots and with 1 MOhm resistors for the LM334 loads put the LM334 output voltage at closest: with three DPots per leg
    //        #define NON_LSB_DPOT_1_B0REF_STARTVALUE 117 //or ( MAX_DPOT_SETTG / 2 )   //this settingValue in digipots and with 1 MOhm resistors for the LM334 loads put the LM334 output voltage at closest: with two DPots per leg
    #endif
    #if ( ( DPOTS_PER_LM334_LEG > 2 ) || ( DPOTS_PER_BRIDGED_BARE_LEG > 2 ) || ( DPOTS_PER_UNBRIDGED_BARE_LEG > 2 ) )
        #define NON_LSB_DPOT_2_B0SIG_PIN ( 9 + 64 )         // third digital pot of signal leg CS line connected to here.  coarse adjust B positive (signal) leg
        #define NON_LSB_DPOT_2_B0SIG_STARTVALUE 0  //or ( MAX_DPOT_SETTG / 2 )  //this settingValue in digipots and with 1 MOhm resistors for the LM334 loads put the LM334 output voltage at closest
    #endif
    #if ( ( DPOTS_PER_LM334_LEG > 2 ) || ( DPOTS_PER_BRIDGED_BARE_LEG > 2 ) )
        #define NON_LSB_DPOT_2_B0REF_PIN 9         // third digital pot of reference leg CS line connected to here.  coarse adjust B negative (reference) leg
        #define NON_LSB_DPOT_2_B0REF_STARTVALUE 0  //or ( MAX_DPOT_SETTG / 2 )   //this settingValue in digipots and with 1 MOhm resistors for the LM334 loads put the LM334 output voltage at closest
    #endif
    
    #if ( ( defined ARDUINO_AVR_LEONARDO ) \
        && ( NON_LSB_DPOT_2_B0SIG_PIN == 2 || NON_LSB_DPOT_2_B0SIG_PIN == 3 \
        || NON_LSB_DPOT_1_B0SIG_PIN == 2 || NON_LSB_DPOT_1_B0SIG_PIN == 3 \
        || LSB_DPOT_B0SIG_PIN == 2 || LSB_DPOT_B0SIG_PIN == 3 \
        || NON_LSB_DPOT_2_B0REF_PIN == 2 || NON_LSB_DPOT_2_B0REF_PIN == 3 \
        || NON_LSB_DPOT_1_B0REF_PIN == 2 || NON_LSB_DPOT_1_B0REF_PIN == 3 \
        || LSB_DPOT_B0REF_PIN == 2 || LSB_DPOT_B0REF_PIN == 3 \
        ) )
    //        #if ( LM334_BRIDGES + BARE_DPOT_LEG_BRIDGES > 1 )
    //            #if ( LM334_BRIDGES + BARE_DPOT_LEG_BRIDGES > 2 )
    //                #if ( LM334_BRIDGES + BARE_DPOT_LEG_BRIDGES > 3 )
    //                    #if ( LM334_BRIDGES + BARE_DPOT_LEG_BRIDGES > 4 )
    //                        #if ( LM334_BRIDGES + BARE_DPOT_LEG_BRIDGES > 5 )
    //                            #if ( LM334_BRIDGES + BARE_DPOT_LEG_BRIDGES > 6 )
    //                            #endif
    //                        #endif
    //                    #endif
    //                #endif
    //            #endif
    //        #endif //Expand this if sketch expands
    //    )//This style of compiler preprocessor nested definition doesn't really work.  It is here to show the desired concept
    
        #error "The pins being used for clock and data of the ADC conflict with the I2C pins used by ADS1x15.  See https://www.arduino.cc/en/reference/wire and the Adafruit_ADS1X15-master README.md.  Remove this warning once you are satisfied one way or another"
    #endif
    static int16_t VRsandbox[ NUM_ANALOG_INPUTS - DPOT_LEGS ]; //A spot for reading in the setting of any particular variable resistor potentiometer
    #define VR1_A2 0 //Subscripts for VRsandbox[ ]
    #define VR2_A3 1
    #define VR3_A6 2
    #define VR4_A7 3
    static uint8_t dPotPins[ DPOTS ]; //If I could just figure out how to fill this array here it would sure make for less code clutter
    static uint16_t dPotSettings[ DPOTS ];
    static uint16_t dPotAnchorSettings[ DPOTS ];
    static uint16_t dPotAnchorSettingsEEPROMAddress[ DPOTS ];
    
    #define SOLVENT 2 //Unit subscripts for dPotSettings[ ], dPotAnchorSettings[ ], and dPotAnchorSettingsEEPROMAddress[ ],  Add unit to sub-unit like this: dPotSettings[ SOLVENT + LSB ]
    #define COUNTER_BALANCING_SOLVENT 0 //Unit subscripts for dPotSettings[ ], dPotAnchorSettings[ ], and dPotAnchorSettingsEEPROMAddress[ ],  Add unit to sub-unit like this: dPotSettings[ COUNTER_BALANCING_SOLVENT + LSB ]
    #define LSB 0 //Sub unit subscripts for dPotSettings[ ], dPotAnchorSettings[ ], and dPotAnchorSettingsEEPROMAddress[ ],  Add unit to sub-unit like this: dPotSettings[ SOLVENT + LSB ]
    #define MSB 1 //Sub unit subscripts for dPotSettings[ ], dPotAnchorSettings[ ], and dPotAnchorSettingsEEPROMAddress[ ],  Add unit to sub-unit like this: dPotSettings[ SOLVENT + MSB ]
    static bool pinIsArrayed = true;
    #define THIS_IS_OVERT_PIN_NUMBER_INSTEAD_OF_INDEX false
    #define DONT_CONSOLIDATE_MSB_GROUP_SETTINGS_THIS_TIME false
    /* EEPROM and nonvolatile settings are only available with >8.5, <12.5 Vdc applied to CS pins of MCP4162, which we don't have with mere Arduino: */
    #define MATCHING_TO_SIGNAL_LEG true
#endif

#if ( OUTBOARDS_PLOTTED > 0 )
#define SCALE_FACTOR_TO_PROMOTE_LOW_RES_ADC_TO_SAME_SCALE ( HIGHEST_BIT_RES_FROM_HIGHEST_SENSI_OUTBOARD_ADC - ANALOG_INPUT_BITS_OF_BOARD )
#else
#define SCALE_FACTOR_TO_PROMOTE_LOW_RES_ADC_TO_SAME_SCALE 0
#endif

/*
  DEFINING INDEX_OF_INBOARDS_NOT_SUPERIMPOSED:
*/

#if defined SUPERIMPOSE_FIRST_INBOARDS_IN_PAIRS \
    && ( SUPERIMPOSE_FIRST_INBOARDS_IN_PAIRS > 0 )
#if ( ( ( SUPERIMPOSE_FIRST_INBOARDS_IN_PAIRS * LEGS_PER_DPOT_STYLE_BRIDGE ) < INBOARDS_PLOTTED ) && ( defined LEGS_PER_DPOT_STYLE_BRIDGE ) ) //use the smaller of the two possibilities
#define INDEX_OF_INBOARDS_NOT_SUPERIMPOSED ( SUPERIMPOSE_FIRST_INBOARDS_IN_PAIRS * LEGS_PER_DPOT_STYLE_BRIDGE )
#else
#define INDEX_OF_INBOARDS_NOT_SUPERIMPOSED INBOARDS_PLOTTED
#endif

#else
#define INDEX_OF_INBOARDS_NOT_SUPERIMPOSED 0
#endif

/*
  DEFINING INDEX_OF_INBOARDS_NOT_PLOTTED:
*/

#define INDEX_OF_INBOARDS_NOT_PLOTTED INBOARDS_PLOTTED

/*
  DEFINING INDEX_OF_OUTBOARDS:
*/
#if ( DPOT_LEGS > INBOARDS_PLOTTED )
#define INDEX_OF_OUTBOARDS DPOT_LEGS
#else
#define INDEX_OF_OUTBOARDS INBOARDS_PLOTTED
#endif

struct previous_readings_only_of_inboards_and_outboards
{
  int32_t CurrentUnmagnifiedReading;
  int32_t PreviousUnmagnifiedReading;
  uint8_t IndexInlinespaceParametersArray;
} typedef previous_readings_only;

//To retrieve bridgeleg readings for non-plotting use such as reading their most recent values while adjusting DPots, you must downconvert them with >> SCALE_FACTOR_TO_PROMOTE_LOW_RES_ADC_TO_SAME_SCALE (shift rights).
previous_readings_only masterReadingsArray[ INDEX_OF_OUTBOARDS + OUTBOARDS_PLOTTED ];

struct linespace_bounds_and_magnify_trace_offsets
{
  uint32_t ZeroOfThisPlotLinespace;
  uint32_t HighLimitOfThisPlotLinespace;
  uint32_t LastSignalPinPlotPoint;
  uint32_t LastReferencePinPlotPointOrLastMagnifiedPlotPoint;
#ifdef MAGNIFICATION_FACTOR
  uint32_t MagnifyAdjustment;
#endif
} typedef linespace_bounds_and_magnify_trace_offsets;

/*
  DEFINING NUMBER_OF_LINESPACES:
*/

#define NUMBER_OF_LINESPACES ( INBOARDS_PLOTTED + OUTBOARDS_PLOTTED - ( INDEX_OF_INBOARDS_NOT_SUPERIMPOSED / 2 ) ) //Each superimposed pair reduces total linespaces by one from total of plotted
linespace_bounds_and_magnify_trace_offsets linespaceParameters[ NUMBER_OF_LINESPACES ]; // INDEX_OF_INBOARDS_NOT_SUPERIMPOSED, being the start index for the not superimposed part of the array is also actually the number of superimposed inboards

static bool graphLine = false;
static uint32_t thisReadingTemp;
static long millisStart;
uint16_t plotterLoops;
#ifdef DEBUG
static char szFull[ ] = {0, 0, 0, 0, 0, 0, 0, 0, 0, 0, 0, 0, 0, 0, 0, 0, 0, 0, 0, 0, 0, 0, 0, 0, 0, 0, 0, 0, 0, 0, 0, 0, \
                         0, 0, 0, 0, 0, 0, 0, 0, 0, 0, 0, 0, 0, 0, 0, 0, 0, 0, 0, 0, 0, 0, 0, 0, 0, 0, 0, 0, 0, 0, 0, 0
                        };
#endif
#define HEIGHT_OF_A_PLOT_LINESPACE ( ( uint32_t )pow( 2, HIGHEST_BIT_RES_FROM_HIGHEST_SENSI_OUTBOARD_ADC ) ) //casting as uint32_t allows calculations properly
#define PLOTTER_MAX_SCALE ( ( uint32_t )( HEIGHT_OF_A_PLOT_LINESPACE * NUMBER_OF_LINESPACES ) )
#define HALF_HEIGHT_OF_A_PLOT_LINESPACE ( HEIGHT_OF_A_PLOT_LINESPACE >> 1 )

#if ( ( defined AUTO_BRIDGE_BALANCING ) && ( defined DIFFERENTIAL ) )
#define HALF_HEIGHT_INBOARD_SCALE_OF_A_PLOT_LINESPACE ( pow( 2, ANALOG_INPUT_BITS_OF_BOARD - 1 ) )
static uint16_t counterForTraceOutOfRangeTooLong[ OUTBOARDS_PLOTTED ]; //Main intent is for DIFFERENTIAL input ADCs. This is also used to prevent infinite loop with AUTO_BRIDGE_BALANCING
#endif
#define HUNDREDTH_PLOTTER_MAX_SCALE ( PLOTTER_MAX_SCALE / 100 );
#ifndef SAMPLE_TIMES
#define SAMPLE_TIMES 1
#elif ( 1 > SAMPLE_TIMES + 0 )
#undef SAMPLE_TIMES
#define SAMPLE_TIMES 1
#endif
/*  development notes to self:
  Is SUPERIMPOSE_FIRST_INBOARDS_IN_PAIRS (1, 2, 3, etc. ) ever needed?
  AUTO_BRIDGE_BALANCING means both initial setup & ongoing adjustment: initial adjustment means setting pots to EEPROM settings or defines settings and for
  sweet spot ADCs it fines tunes during setup and re-stores that in EEPROM
  defined AUTO_BRIDGE_BALANCING should only be allowed to be the case
    with OUTBOARDS_PLOTTED > 0
    and LM334_BRIDGES (?inboard pairs 1, 2, 3, etc. or ADDONs n... ) //Besides being used for auto-balancing, these could be used just to allow a wider range of plant tissue conductance.
    and SUPERIMPOSE_FIRST_INBOARDS_IN_PAIRS (but is this moot?).  The alternative
    to this condition in isolation from bridge balancing is just adjusting to plant resistance instead of
  Bridge balancing should not be needed with those ADCs that need a sweet spot to work.  That sweet spot could be hard wired or manual pot adjusted and only
  bridge LEG adjusting should get done????
  With those ADCs, the digipots should be able to be put in serial and assigned to
  Except that the tempco of the LM334 will then all be on only one leg, thus not able to be balanced out to cancel out, so never mind....
  Possibilities:
  AUTO...BALANCING is invalid w/o ...POTS and ...PARALLELed > 0
  not LM334_BRIDGES - invalidates AUTO...BALANCING
                                  - if inputs are ...PARALLELed > 0 and ...ADDONs exist and INBOARDS > 0, it is for manual pot manipulations while viewing
                                    traces
  So: - define ...PARALLELed = 0 if it is undefined
    - undefine USING...POTS if USING...POTS == 0 or if ...INBOARD == 0 and not AUTO...BALANCING and #defined LEAVE_POT_VALUES_ALONE_DURING_SETUP and #not defined DEBUG, the digipots may be useful in debug then re-compile but why would they need to be
    - undefine AUTO...BALANCING if not USING...POTS, or if not ...ADDONs, or if ...PARALLELed == 0
    - define ...PARALLELed = 0 if ...ADDONs == 0, or if not AUTO...BALANCING and ...INBOARD == 0 while USING...POTS
*/
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
void loop()
{
    int16_t potentialMSBoffset;
    int16_t savedMSBsettingsThisLeg;
    int32_t potentialLSBoffset;
    int16_t savedLSBsettingsThisLeg;
#if ( ( not defined MINIMIZE_COMMUNICATIONS_CLUTTER_FOR_HIGHER_MAX_SPEED_ONLY_COMPATIBLE_FOR_OFFICIAL_ARDUINO_IDE ) || ( MINIMIZE_COMMUNICATIONS_CLUTTER_FOR_HIGHER_MAX_SPEED_ONLY_COMPATIBLE_FOR_OFFICIAL_ARDUINO_IDE == false ) )
#if ( DPOTS_IN_ALL_LM334_BRIDGES + DPOTS_IN_ALL_BARE_LEG_BRIDGES + DPOTS_IN_ALL_BARE_LEGS_UNBRIDGED > 0 )
  for( uint8_t csIndex = 0; csIndex < DPOTS; csIndex++ )
  {
    Serial.print( F( "dPotSettings[" ) );
    Serial.print( dPotPins[ csIndex ] );
    Serial.print( F( "]=" ) );
    Serial.print( dPotSettings[ csIndex ] );
    if( csIndex < DPOTS - 1 )
      Serial.print( F( ",. " ) );
    else
      Serial.print( F( ",. " ) );
  }
#endif
#endif
  for( plotterLoops = 0; plotterLoops < 500 / 3; plotterLoops++ )
  {
    millisStart = millis();
    //        if( graphLine ) thisReadingTemp = 0;
    //        else thisReadingTemp = PLOTTER_MAX_SCALE;
    //        Serial.print( thisReadingTemp ); //This was originally last printed in the group.  It needs to be first instead so the line can be "notched" horizontally without needing to reprint all values.
    //        Serial.print( F( " " ) );
    //        readAndPlotFromAllADCsInAndOutboard( thisReadingTemp );
    readAndPlotFromAllADCsInAndOutboard( graphLine ? 0 : PLOTTER_MAX_SCALE );
#ifdef AUTO_BRIDGE_BALANCING //Unsure of how to relate this macro and macro DIFFERENTIAL
    for( uint8_t whichOutboardADCindex = 0; whichOutboardADCindex < OUTBOARDS_PLOTTED; whichOutboardADCindex++ )
    {
      if( masterReadingsArray[ INDEX_OF_OUTBOARDS + whichOutboardADCindex ].CurrentUnmagnifiedReading >= HEIGHT_OF_A_PLOT_LINESPACE - 1 )
      {
    #if ( ( not defined MINIMIZE_COMMUNICATIONS_CLUTTER_FOR_HIGHER_MAX_SPEED_ONLY_COMPATIBLE_FOR_OFFICIAL_ARDUINO_IDE ) || ( MINIMIZE_COMMUNICATIONS_CLUTTER_FOR_HIGHER_MAX_SPEED_ONLY_COMPATIBLE_FOR_OFFICIAL_ARDUINO_IDE == false ) )
            Serial.print( F( " reading apparently maxed out " ) );
    #endif
    #if ( defined DIFFERENTIAL ) && ( defined LOOP_COUNTER_LIMIT_THAT_TRACE_IS_ALLOWED_TO_BE_OFF_CENTER )
            if( ++counterForTraceOutOfRangeTooLong[ whichOutboardADCindex ] > LOOP_COUNTER_LIMIT_THAT_TRACE_IS_ALLOWED_TO_BE_OFF_CENTER )
            {
                potentialMSBoffset = 1;
                goto NeedsAdjustment;
            }
    #else
        ;
    #endif
      }
      else if( masterReadingsArray[ INDEX_OF_OUTBOARDS + whichOutboardADCindex ].CurrentUnmagnifiedReading == 0 ) //means reference leg is higher
      { ;
    #if ( ( not defined MINIMIZE_COMMUNICATIONS_CLUTTER_FOR_HIGHER_MAX_SPEED_ONLY_COMPATIBLE_FOR_OFFICIAL_ARDUINO_IDE ) || ( MINIMIZE_COMMUNICATIONS_CLUTTER_FOR_HIGHER_MAX_SPEED_ONLY_COMPATIBLE_FOR_OFFICIAL_ARDUINO_IDE == false ) )
            Serial.print( F( " reading apparently zeroed out " ) );
    #endif
    #if ( defined DIFFERENTIAL ) && ( defined LOOP_COUNTER_LIMIT_THAT_TRACE_IS_ALLOWED_TO_BE_OFF_CENTER )
            if( 0 - --counterForTraceOutOfRangeTooLong[ whichOutboardADCindex ] > LOOP_COUNTER_LIMIT_THAT_TRACE_IS_ALLOWED_TO_BE_OFF_CENTER )
            {
              //Process: lower reference leg if it is higher than commonmode... level until it reaches commonmode..., then raise signal leg until can't raise it any more, then resume to lower reference leg until can't lower it any more
              //                setSignalBridgeLegInput( whichOutboardADCindex ); // Instead maybe use AdjustBridgeOutput ative( bridge );
                potentialMSBoffset = -1;
NeedsAdjustment:;
        #if ( ( not defined MINIMIZE_COMMUNICATIONS_CLUTTER_FOR_HIGHER_MAX_SPEED_ONLY_COMPATIBLE_FOR_OFFICIAL_ARDUINO_IDE ) || ( MINIMIZE_COMMUNICATIONS_CLUTTER_FOR_HIGHER_MAX_SPEED_ONLY_COMPATIBLE_FOR_OFFICIAL_ARDUINO_IDE == false ) )
                  Serial.print( F( "for longer than allowed " ) );
        #endif
//                configureForSignalLegWithBridgeIndexIncludingNonBridgedLegs( whichOutboardADCindex );
//procedure to adjust leg: check reference leg to see if it is off in the same direction of best CM level.  if not, work on signal leg after reference leg is set to best CM
                if( !startMSBsettingForCalculatingSettingUnitsPerAnalogInputUnit[ INDEX_OF_OUTBOARDS + whichOutboardADCindex ] )
                {
                    startMSBsettingForCalculatingSettingUnitsPerAnalogInputUnit[ INDEX_OF_OUTBOARDS + whichOutboardADCindex ] = MSB_SETTINGS_TOTAL_SIGNAL_THIS_BRIDGE( whichOutboardADCindex );
                }
                else
                {
/*FUTURE: recalculate setting units per analog unit*/
                    startLSBsettingForCalculatingSettingUnitsPerAnalogInputUnit[ INDEX_OF_OUTBOARDS + whichOutboardADCindex ] = \
                    dPotSettings[ whatIsSignalLSBdPotIndexThisBridge( whichOutboardADCindex ) ];
                    incomingInboardAnalogLevelSignal[ whatIsSignalLegThisBridge( whichOutboardADCindex ) ] = masterReadingsArray[ whatIsSignalLegThisBridge( whichOutboardADCindex ) ].CurrentUnmagnifiedReading >> SCALE_FACTOR_TO_PROMOTE_LOW_RES_ADC_TO_SAME_SCALE;
                }

//                potentialMSBoffset = ( int16_t )\
//( ( signed )COMMON_MODE_LEVEL_FOR_MAX_GAIN_AS_READ_RAW_BY_INBOARD_ANALOG - ( masterReadingsArray[ whatIsSignalLegThisBridge( whichOutboardADCindex ) ].CurrentUnmagnifiedReading >> SCALE_FACTOR_TO_PROMOTE_LOW_RES_ADC_TO_SAME_SCALE ) ) / ( analogInputUnitsTimes64PerMSBLegSettingUnit[ whatIsSignalLegThisBridge( whichOutboardADCindex ) ] / ( signed )pow( 2, BITS_TO_LEFT_SHIFT_TO_KEEP_HIGH_RESOLUTION ) );
              if( potentialMSBoffset ) //> 1 ) || ( potentialMSBoffset < -1 ) ) 
              {
/*
                    Serial.print( F( "Line <4081>potentialMSBoffset=<" ) );
                    Serial.print( potentialMSBoffset );
                    Serial.print( F( "> masterReadingsArray[ whatIsSignalLegThisBridge( whichOutboardADCindex ) ].CurrentUnmagnifiedReading >> SCALE_FACTOR_TO_PROMOTE_LOW_RES_ADC_TO_SAME_SCALE=<" ) );
                    Serial.print( masterReadingsArray[ whatIsSignalLegThisBridge( whichOutboardADCindex ) ].CurrentUnmagnifiedReading >> SCALE_FACTOR_TO_PROMOTE_LOW_RES_ADC_TO_SAME_SCALE );
                    Serial.print( F( "> ( signed )( pow( <2>, ANALOG_INPUT_BITS_OF_BOARD ) * ( <100> - PERCENT_OF_LINESPACE_MAGNIFIED_VIEW_SKIPS_WHEN_REPOSITIONED_WHEN_LINESPACE_LIMITS_GET_EXCEEDED ) ) / <100>=<" ) );
                    Serial.print( ( ( signed )pow( 2, ANALOG_INPUT_BITS_OF_BOARD ) * ( 100 - PERCENT_OF_LINESPACE_MAGNIFIED_VIEW_SKIPS_WHEN_REPOSITIONED_WHEN_LINESPACE_LIMITS_GET_EXCEEDED ) ) / 100 );
                    Serial.print( F( "> ( masterReadingsArray[ whatIsSignalLegThisBridge( whichOutboardADCindex ) ].CurrentUnmagnifiedReading >> SCALE_FACTOR_TO_PROMOTE_LOW_RES_ADC_TO_SAME_SCALE ) - ( ( pow( <2>, ANALOG_INPUT_BITS_OF_BOARD ) * ( <100> - PERCENT_OF_LINESPACE_MAGNIFIED_VIEW_SKIPS_WHEN_REPOSITIONED_WHEN_LINESPACE_LIMITS_GET_EXCEEDED ) ) / <100> )=<" ) );
                    Serial.print( ( masterReadingsArray[ whatIsSignalLegThisBridge( whichOutboardADCindex ) ].CurrentUnmagnifiedReading >> SCALE_FACTOR_TO_PROMOTE_LOW_RES_ADC_TO_SAME_SCALE ) - ( ( ( signed )pow( 2, ANALOG_INPUT_BITS_OF_BOARD ) * ( 100 - PERCENT_OF_LINESPACE_MAGNIFIED_VIEW_SKIPS_WHEN_REPOSITIONED_WHEN_LINESPACE_LIMITS_GET_EXCEEDED ) ) / 100 ) );
                    Serial.print( F( ">.analogInputUnitsTimes64PerMSBLegSettingUnit[ whatIsSignalLegThisBridge( whichOutboardADCindex ) ]=<" ) );
                    Serial.print( analogInputUnitsTimes64PerMSBLegSettingUnit[ whatIsSignalLegThisBridge( whichOutboardADCindex ) ] );
                    Serial.print( F( "> ( analogInputUnitsTimes64PerMSBLegSettingUnit[ whatIsSignalLegThisBridge( whichOutboardADCindex ) ] / ( signed )pow( <2>, BITS_TO_LEFT_SHIFT_TO_KEEP_HIGH_RESOLUTION ) )=<" ) );
                    Serial.print( ( analogInputUnitsTimes64PerMSBLegSettingUnit[ whatIsSignalLegThisBridge( whichOutboardADCindex ) ] / ( signed )pow( 2, BITS_TO_LEFT_SHIFT_TO_KEEP_HIGH_RESOLUTION ) ) );
                    Serial.print( F( ">." ) );
*/
//May want to Calculate new analogInputUnitsTimes64PerMSBLegSettingUnit based on level response of previous instruction
//                    startMSBsettingForCalculatingSettingUnitsPerAnalogInputUnit[ INDEX_OF_OUTBOARDS + whichOutboardADCindex ] = MSB_SETTINGS_TOTAL_SIGNAL_THIS_BRIDGE( whichOutboardADCindex );
//analogInputUnitsTimes64PerMSBLegSettingUnit[ whatIsSignalLegThisBridge( whichOutboardADCindex ) ] = \
//( ( ( bestOfFour( whatIsSignalLegThisBridge( whichOutboardADCindex ) ) ) - ( masterReadingsArray[ whatIsSignalLegThisBridge( whichOutboardADCindex ) ].CurrentUnmagnifiedReading >> SCALE_FACTOR_TO_PROMOTE_LOW_RES_ADC_TO_SAME_SCALE ) ) * ( signed )pow( 2, BITS_TO_LEFT_SHIFT_TO_KEEP_HIGH_RESOLUTION ) ) / \
//( MSB_SETTINGS_TOTAL_SIGNAL_THIS_BRIDGE( whichOutboardADCindex ) - savedMSBsettingsThisLeg );
/*
                Serial.print( F( "New analogInputUnitsTimes64PerMSBLegSettingUnit would be=<" ) );
                Serial.print( ( ( ( bestOfFour( whatIsSignalLegThisBridge( whichOutboardADCindex ) ) ) - ( masterReadingsArray[ whatIsSignalLegThisBridge( whichOutboardADCindex ) ].CurrentUnmagnifiedReading >> SCALE_FACTOR_TO_PROMOTE_LOW_RES_ADC_TO_SAME_SCALE ) ) * ( signed )pow( 2, BITS_TO_LEFT_SHIFT_TO_KEEP_HIGH_RESOLUTION ) ) / \
( MSB_SETTINGS_TOTAL_SIGNAL_THIS_BRIDGE( whichOutboardADCindex ) - savedMSBsettingsThisLeg ) );
                Serial.print( F( ">." ) ); */
                offsetMSBdPotOrGroupValueUsingIndicesOnly( whatIsFirstSignalMSBindexThisBridge( whichOutboardADCindex ), potentialMSBoffset );
              }
              else
              {
/*savedLSBsettingsThisLeg = */
//                potentialLSBoffset = \
//( legLSBsettingUnitsTimes64PerAnalogInputUnit[ whatIsSignalLegThisBridge( whichOutboardADCindex ) ] * ( \
//( masterReadingsArray[ whatIsSignalLegThisBridge( whichOutboardADCindex ) ].CurrentUnmagnifiedReading >> SCALE_FACTOR_TO_PROMOTE_LOW_RES_ADC_TO_SAME_SCALE ) \
//- \
//( signed )COMMON_MODE_LEVEL_FOR_MAX_GAIN_AS_READ_RAW_BY_INBOARD_ANALOG \
//) ) / ( signed )pow( 2, BITS_TO_LEFT_SHIFT_TO_KEEP_HIGH_RESOLUTION );
                Serial.print( F( "Line<4108>Needs LSB offset of=<" ) );
                Serial.print( potentialLSBoffset );
                Serial.print( F( ">." ) );
                offsetMSBdPotOrGroupValueUsingIndicesOnly( whatIsSignalLSBdPotIndexThisBridge( whichOutboardADCindex ), potentialLSBoffset );
                  potentialLSBoffset = 0;
              }
              plotterLoops = 0;
            }
    #else
        ;
    #endif
      }
    #ifdef DIFFERENTIAL
          else if( counterForTraceOutOfRangeTooLong ) //Trace has been out of range but now back in.  Stick it where we want it
          { //TODO: FIXME Debug why this quarrantined code does not work properly
//            potentialLSBoffset = ( legLSBsettingUnitsTimes64PerAnalogInputUnit[ whatIsSignalLegThisBridge( whichOutboardADCindex ) ] * \
//            ( ( signed )( HALF_HEIGHT_OF_A_PLOT_LINESPACE >> SCALE_FACTOR_TO_PROMOTE_LOW_RES_ADC_TO_SAME_SCALE ) - \
//            ( masterReadingsArray[ INDEX_OF_OUTBOARDS + whichOutboardADCindex ].CurrentUnmagnifiedReading >> SCALE_FACTOR_TO_PROMOTE_LOW_RES_ADC_TO_SAME_SCALE ) ) ) / ( signed )pow( 2, BITS_TO_LEFT_SHIFT_TO_KEEP_HIGH_RESOLUTION );
//            offsetMSBdPotOrGroupValueUsingIndicesOnly( whatIsSignalLSBdPotIndexThisBridge( whichOutboardADCindex ), potentialLSBoffset / HIGHEST_SENSI_PGA_GAIN_FACTOR );
            offsetMSBdPotOrGroupValueUsingIndicesOnly( whatIsSignalLSBdPotIndexThisBridge( whichOutboardADCindex ), counterForTraceOutOfRangeTooLong[ whichOutboardADCindex ] > 0 ? 1 : counterForTraceOutOfRangeTooLong[ whichOutboardADCindex ] < 0 ? -1 : 0);
            counterForTraceOutOfRangeTooLong[ whichOutboardADCindex ] = 0;
          }
    #endif
    }
#endif
    //        Serial.println();
    /* The following commented code can be used for keyboard input */
#ifdef DEBUG
            char nextChar;
            nextChar = 0;
            while( Serial.available() )
            {
      //            pinMode( LED_BUILTIN, OUTPUT );                // These lines for blinking the LED are here if you want the LED to blink when data is rec'd
      //            digitalWrite( LED_BUILTIN, HIGH );             // These lines for blinking the LED are here if you want the LED to blink when data is rec'd
                nextChar = (char)Serial.read();
                if( nextChar != 0xD && nextChar != 0xA )
                {
                    szFull[ strlen( szFull ) + 1 ] = 0;
                    szFull[ strlen( szFull ) ] = nextChar;
                }
                else
                {
                    if( Serial.available() ) Serial.read();
                    nextChar = 0;
                }
            }
      //        digitalWrite( LED_BUILTIN, LOW );                  // These lines for blinking the LED are here if you want the LED to blink when data is rec'd
            if( !( szFull[ 0 ] == 0 || nextChar != 0 ) )        //The way this and while loop is set up allows reception of lines with no endings but at a timing cost of one loop()
            {
                #ifdef DEBUG
                    while( !Serial ); // wait for serial port to connect. Needed for Leonardo's native USB
                    Serial.print( F( "Received " ) );
                    Serial.println( szFull );
                #endif
        #if defined LEGS_PER_DPOT_STYLE_BRIDGE
                uint8_t DIGITAL_POT_;
                int offset_integer;
                if( szFull[ 1 ] == 'D' || szFull[ 1 ] == 'd' ) szFull[ 1 ] = '-';
                else if( szFull[ 1 ] == 'U' || szFull[ 1 ] == 'u' ) szFull[ 1 ] = '+';
                if( szFull[ 1 ] == '-' )
                {
                    if( szFull[ 2 ] == 0 )
                        offset_integer = -1;
                    else
                        offset_integer = 0 - atoi( &szFull[ 2 ] );
                }
                else if( szFull[ 1 ] == '+' )
                {
                    if( szFull[ 2 ] == 0 )
                        offset_integer = 1;
                    else
                        offset_integer = atoi( &szFull[ 2 ] );
                }
                else goto NoPotChange;
                if( offset_integer > MAX_DPOT_SETTG || offset_integer < 0 - MAX_DPOT_SETTG ) goto NoPotChange;
                if( szFull[ 0 ] == '1' ) DIGITAL_POT_ = dPotPins[ 0 ];
                else if( szFull[ 0 ] == '2' ) DIGITAL_POT_ = dPotPins[ 1 ];
                else if( szFull[ 0 ] == '3' ) DIGITAL_POT_ = dPotPins[ 2 ];
                else if( szFull[ 0 ] == '4' ) DIGITAL_POT_ = dPotPins[ 3 ];
                else if( szFull[ 0 ] == '5' ) DIGITAL_POT_ = dPotPins[ 4 ];
                else if( szFull[ 0 ] == '6' ) DIGITAL_POT_ = dPotPins[ 5 ];
                else goto NoPotChange;
                indexOfThisDPotCSpinInDPotArrays = atoi( &szFull[ 0 ] ) - 1;
                configureFromDPotIndex();
                offsetMSBdPotOrGroupValueUsingIndicesOnly( DIGITAL_POT_, offset_integer ); //configureFrom...() and configureFor...() must already be ran
                Serial.print( F( "Dpot " ) );
                Serial.print( DIGITAL_POT_ );
                Serial.print( F( " now set to " ) );
                Serial.println( dPotSettings[ atoi( &szFull[ 0 ] ) ] );
      NoPotChange:
        #endif
                szFull[ 0 ] = 0;
//                #ifdef DEBUG
                    while( !Serial ); // wait for serial port to connect. Needed for Leonardo's native USB
                    Serial.println();
//                #endif
            }
#endif
/*    */
#if defined ( TEST_STEP_UP_DOWN ) //This may be defunct
    for( uint8_t bridge = 0; bridge < LM334_BRIDGES; bridge++ )
    {
#if ( TEST_STEP_UP_DOWN == SINGLESIDE )
      if( potstepdirection )
      { //adjustBridgeOutputPositive until maxed
        if( !adjustBridgeOutputPositive( bridge ) )
        {
          potstepdirection = false;
          adjustBridgeOutputNegative( bridge );
        }
      }
      else
      {
        if( !adjustBridgeOutputNegative( bridge ) )
        {
          potstepdirection = true;
          adjustBridgeOutputPositive( bridge );
        }
      }
#elif ( TEST_STEP_UP_DOWN == COMMONMODE )
      AdjustWholeBridgeCommonmode( bridge );
#else
      ;//in case preprocessor conditions cause no other code to form in here
#endif
    }
#endif
    for( uint8_t dPotIndex = 0; dPotIndex < DPOTS; dPotIndex++) //THIS ASSUMES THE ABOVE CONSTRUCT FILLS BOTH ARRAYS COMPLETELY
    {
#ifdef NUM_DIGITAL_PINS
      if( ( dPotSettings[ dPotIndex ] > MAX_DPOT_SETTG ) || ( dPotPins[ dPotIndex ] > NUM_DIGITAL_PINS ) ) break;  //The protection against arrays not fully set up
#else
      if( dPotSettings[ dPotIndex ] > MAX_DPOT_SETTG ) break;  //The protection against arrays not fully set up
#endif
        writeSettingToAsingleDPot( dPotPins[ dPotIndex ], dPotSettings[ dPotIndex ], THIS_IS_OVERT_PIN_NUMBER_INSTEAD_OF_INDEX );  //b/c the analog pin array not set up, this needs pin numbers like this, not pin indexes
    }
    while( millis() - millisStart < MIN_WAIT_TIME_BETWEEN_PLOT_POINTS_MS )
    { //acquire and process not-plotted readings of inboard analog pins that get used for digipot auto-balancing FUTURE TODO
      ;//or just wait.
    }
  }
  while( !Serial ); // wait for serial port to connect. Needed for Leonardo's native USB
  if( !graphLine )
  { //going down
//The next line quarantined places the outboard ADCs at the bottom of the screen, which I felt was not the best way.  It is closely related to other lines that must be quarantined also
//    for( uint8_t linespaceParametersIndex = 0; linespaceParametersIndex < NUMBER_OF_LINESPACES; linespaceParametersIndex++ )
    for( uint8_t linespaceParametersIndex = NUMBER_OF_LINESPACES - 1; linespaceParametersIndex != 255; linespaceParametersIndex-- )
    {
#if ( ( not defined MINIMIZE_COMMUNICATIONS_CLUTTER_FOR_HIGHER_MAX_SPEED_ONLY_COMPATIBLE_FOR_OFFICIAL_ARDUINO_IDE ) || ( MINIMIZE_COMMUNICATIONS_CLUTTER_FOR_HIGHER_MAX_SPEED_ONLY_COMPATIBLE_FOR_OFFICIAL_ARDUINO_IDE == false ) )
      Serial.print( F( " upper bounds of this linespace" ) );
#endif
      Serial.print( F( " " ) );
      Serial.print( linespaceParameters[ linespaceParametersIndex ].HighLimitOfThisPlotLinespace );
      replotLastValuesForAllTraces( true );
#if ( ( not defined MINIMIZE_COMMUNICATIONS_CLUTTER_FOR_HIGHER_MAX_SPEED_ONLY_COMPATIBLE_FOR_OFFICIAL_ARDUINO_IDE ) || ( MINIMIZE_COMMUNICATIONS_CLUTTER_FOR_HIGHER_MAX_SPEED_ONLY_COMPATIBLE_FOR_OFFICIAL_ARDUINO_IDE == false ) )
      Serial.print( F( " lower bounds of this linespace" ) );
#endif
      Serial.print( F( " " ) );
      Serial.print( linespaceParameters[ linespaceParametersIndex ].ZeroOfThisPlotLinespace );
      replotLastValuesForAllTraces( true );
    }
  }
  else
    plotTimingLineGoingUp();

  graphLine = !graphLine; // graphLine started as false, so it becomes true here on the first complementing of it
}
